SSominHUN/NESDev/Thesis/figures/Mario-Duckhunt-cartage.jpg

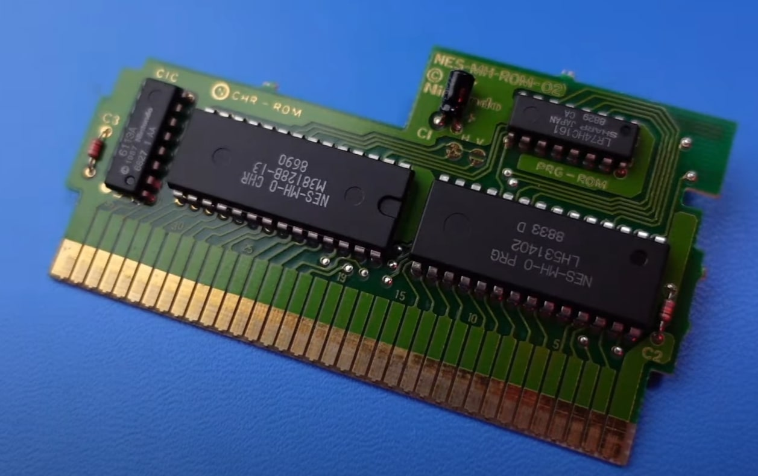
Thesis/figures/Mario-Duckhunt-cartage.jpg
