SSominHUN/NESDev/Thesis/figures/Mario-Patterns.jpg

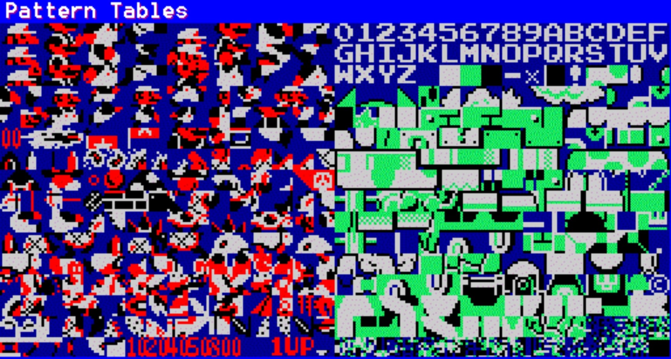
Thesis/figures/Mario-Patterns.jpg
