SSominHUN/NESDev/Thesis/figures/NES-motherboard-lines.jpg

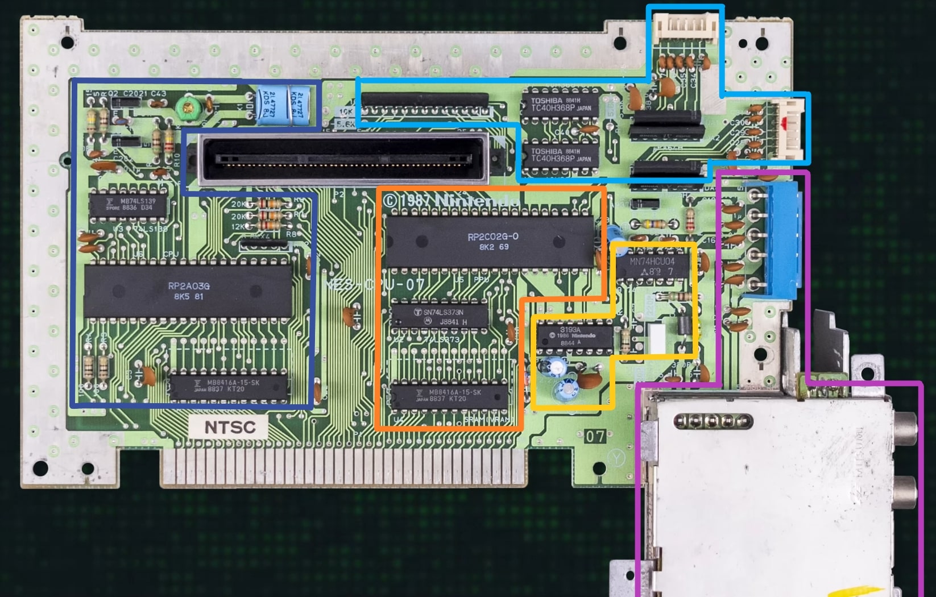
Thesis/figures/NES-motherboard-lines.jpg
