SSominHUN/NESDev/Thesis/figures/sprite-rendering-FSM-v2.png

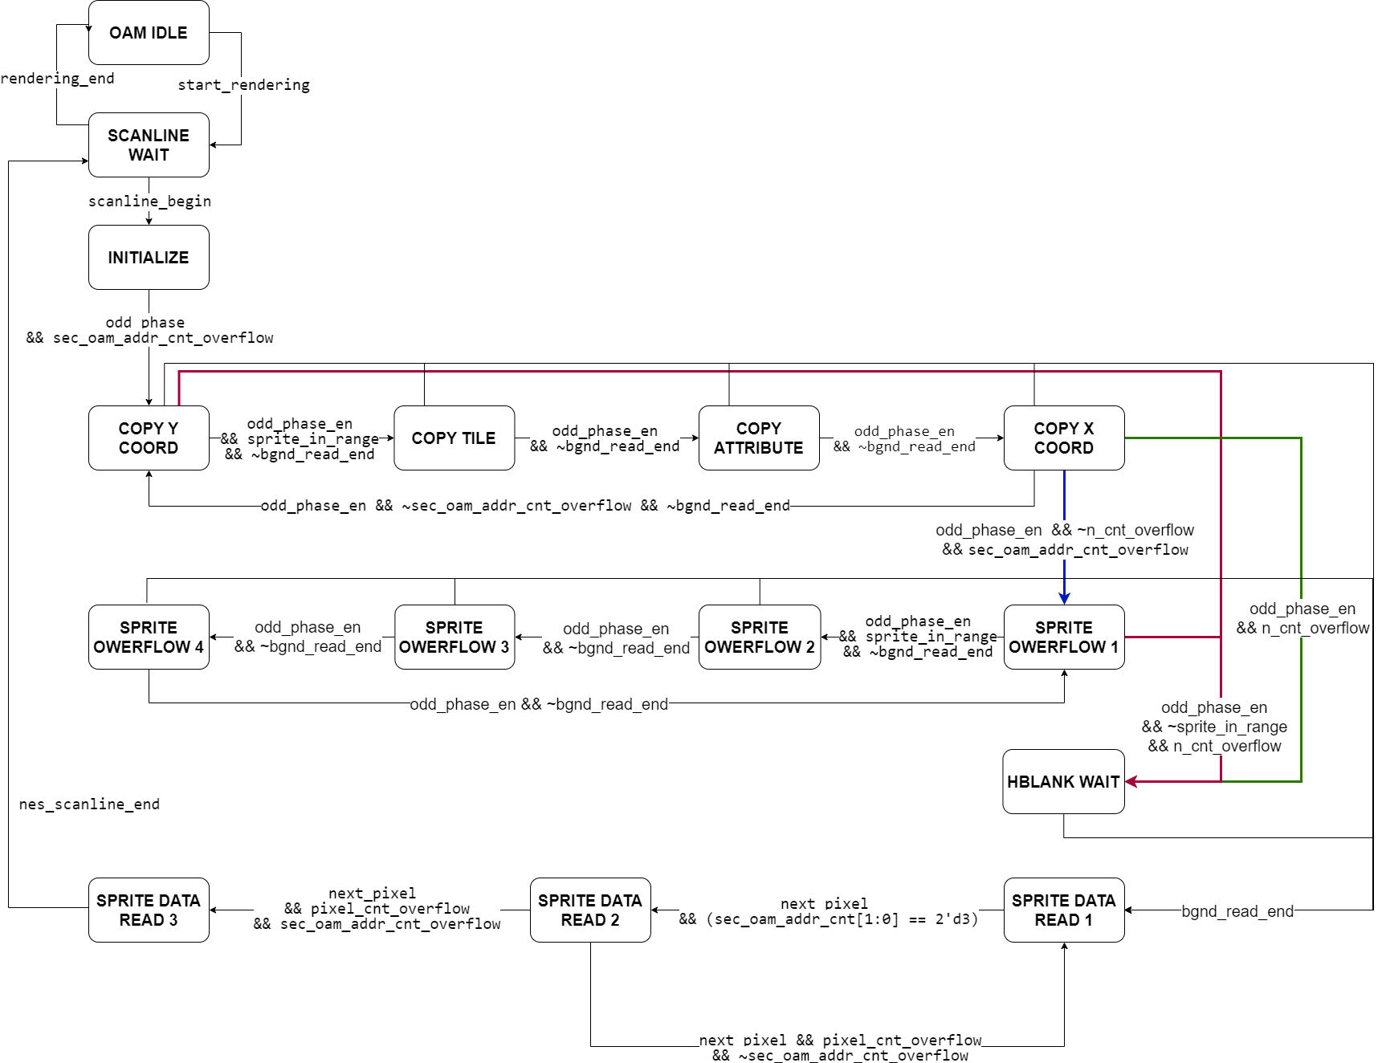
Thesis/figures/sprite-rendering-FSM-v2.png
