SSominHUN/NESDev/Thesis/figures/NES-components-top-1.png

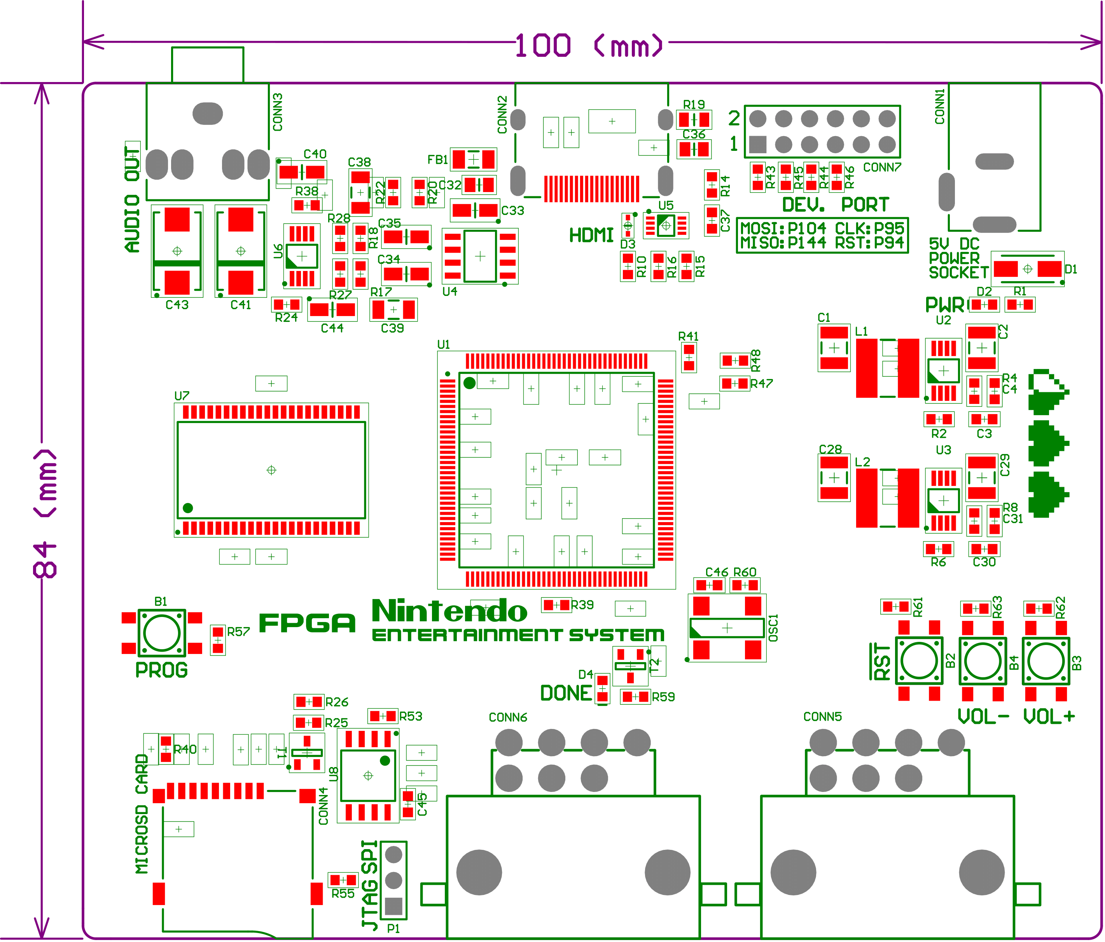
Thesis/figures/NES-components-top-1.png
