SSominHUN/NESDev/NES-pcb/Altium/Doc/FPGA_NES_SCH.PDF

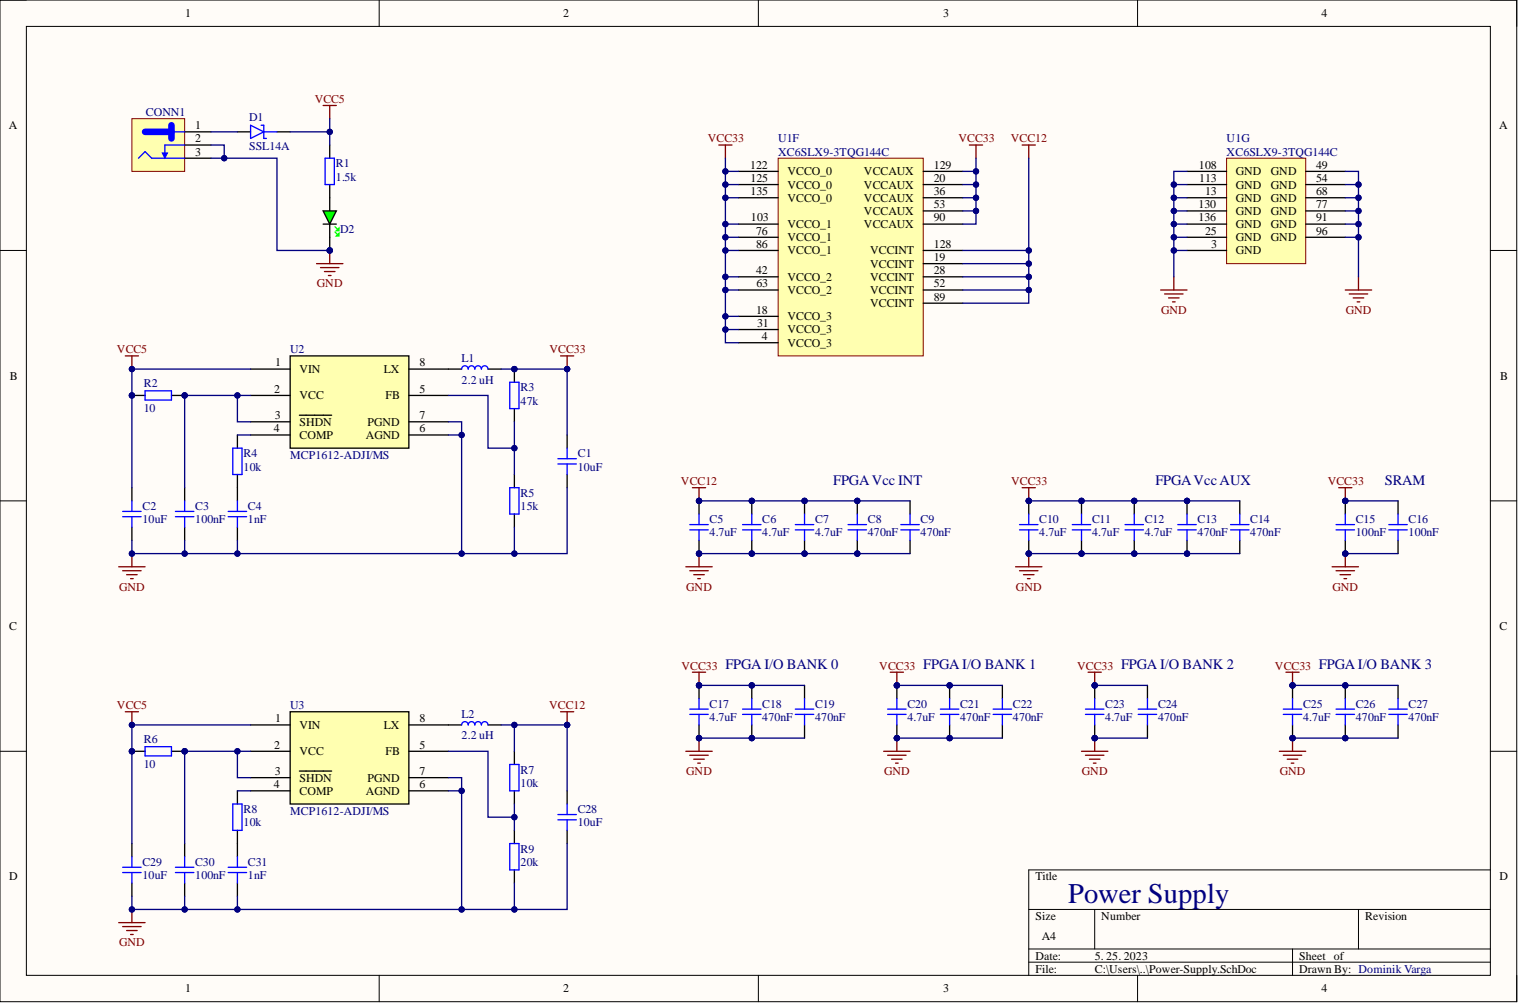
[picture p55: page 1]

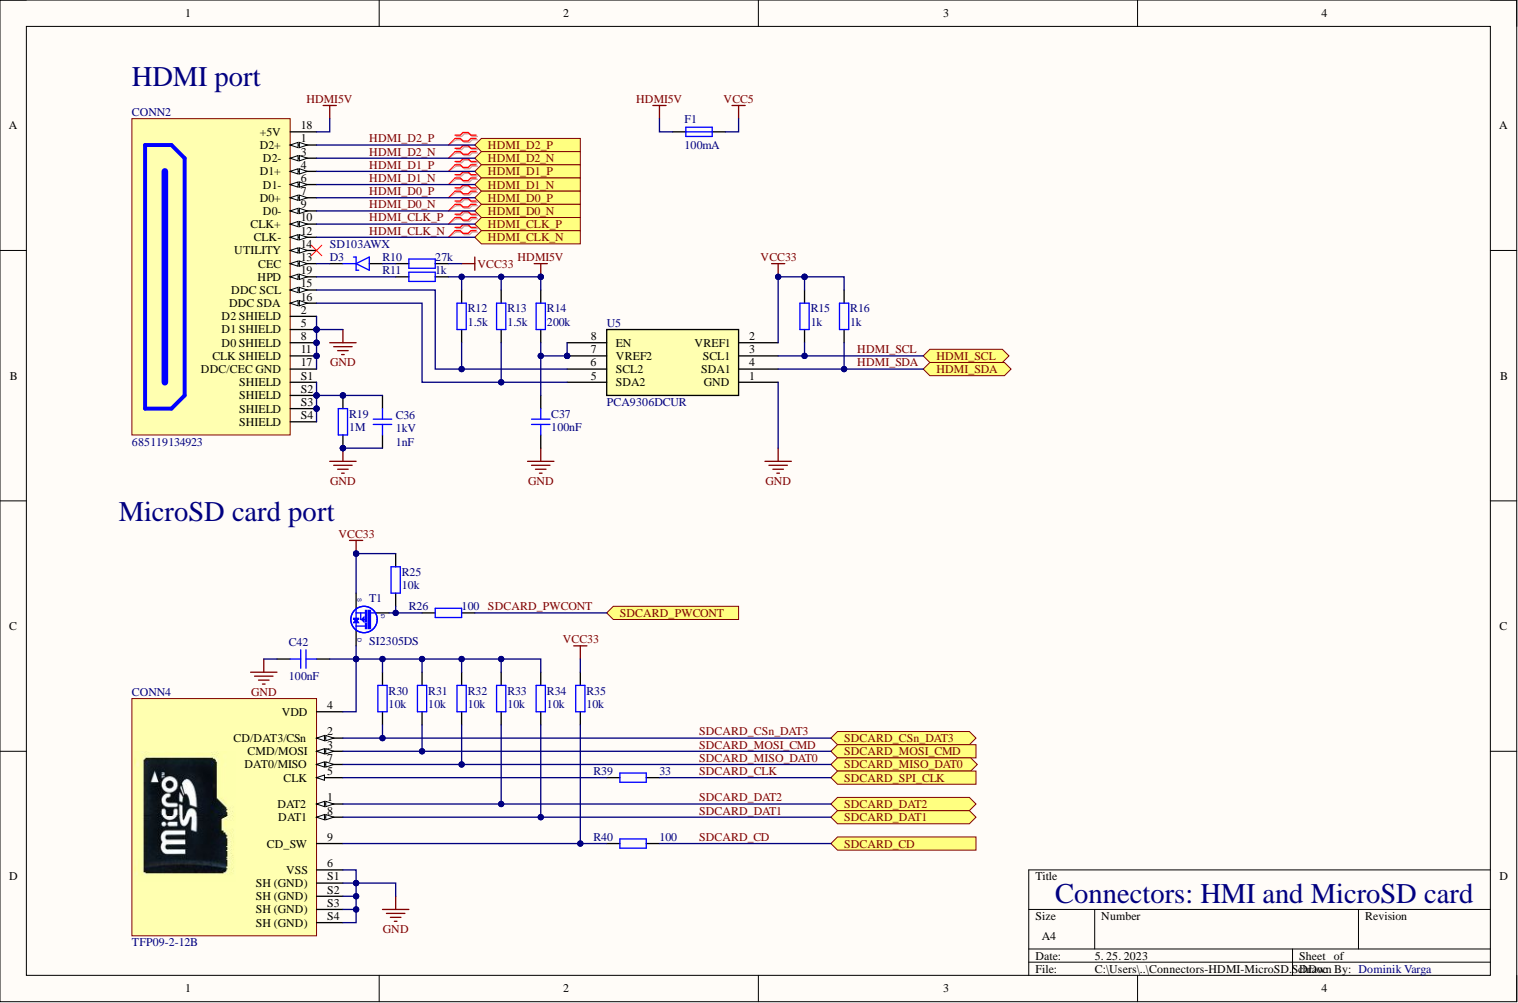
[picture p56: page 2]

Title
Connectors: HMI and MicroSD card

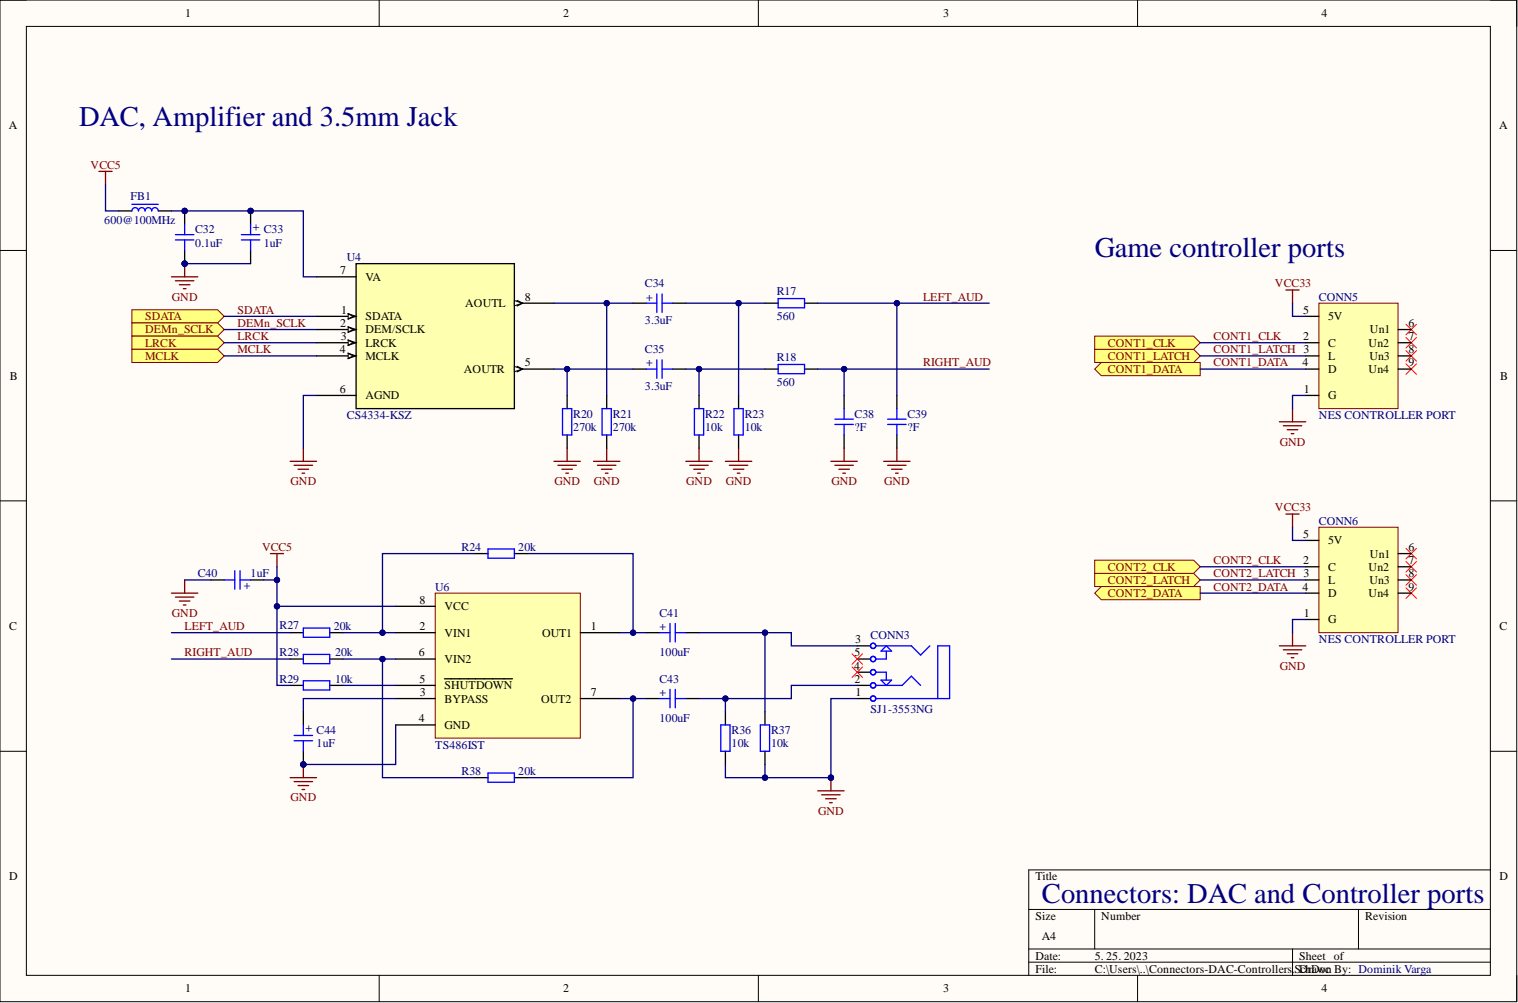
[picture p57: page 3]

DAC, Amplifier and 3.5mm Jack

VCC 8

VIN2 6 | C43

SHUTDOWN 5
BYPASS 3

GND 4

Title
Connectors: DAC and Controller ports

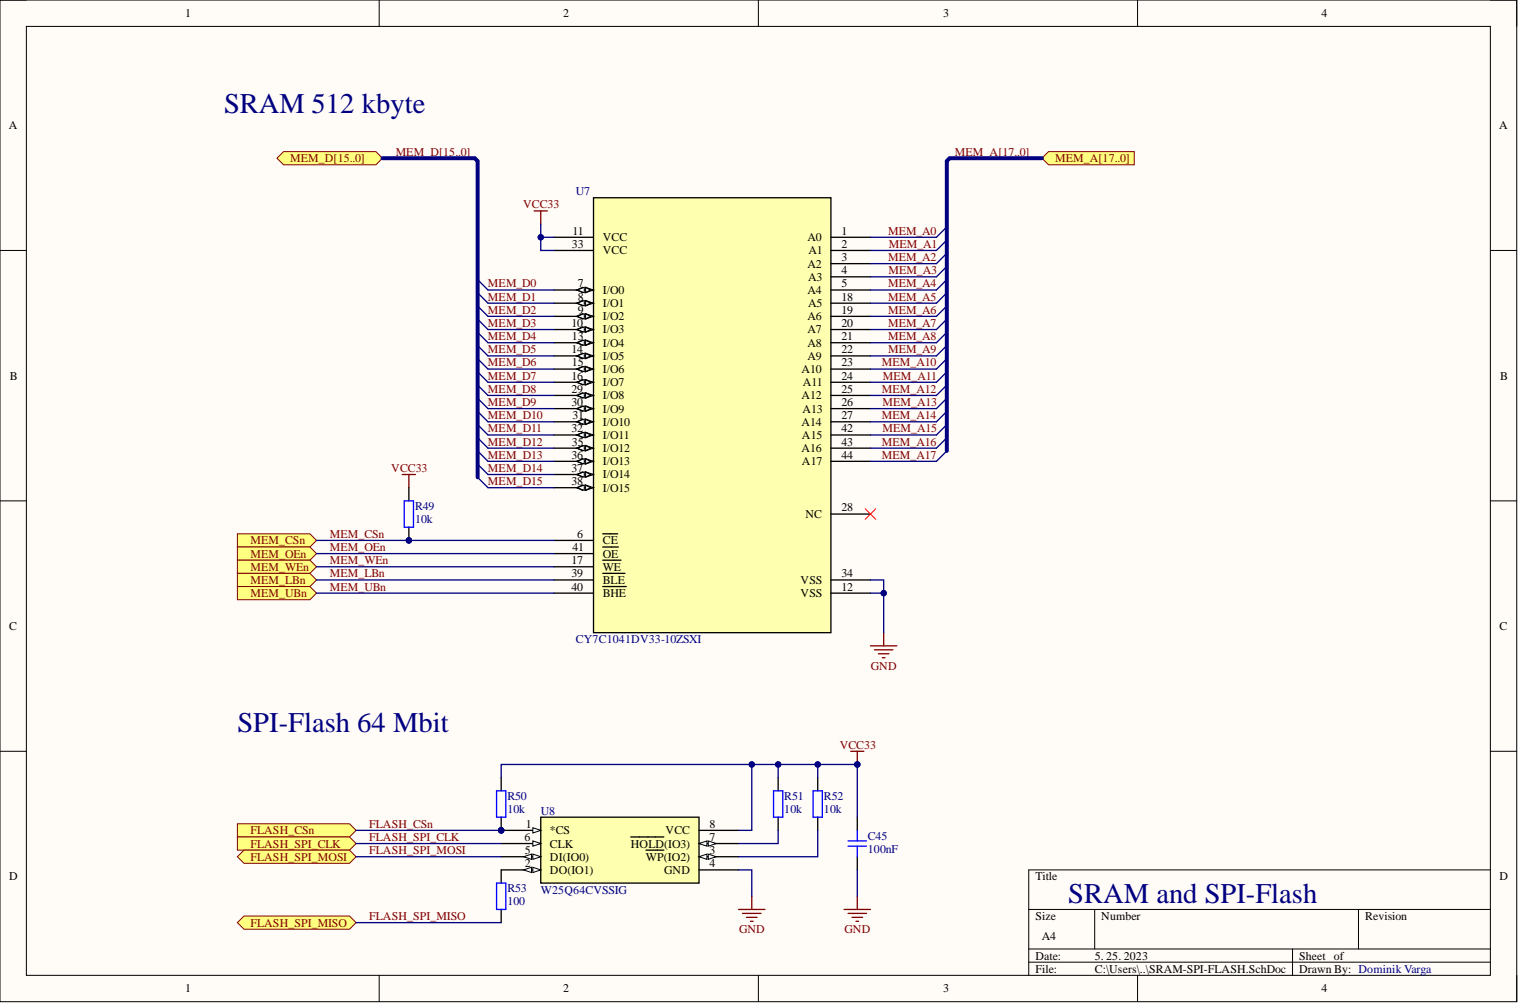
[picture p58: page 4]

Title
SRAM and SPI-Flash

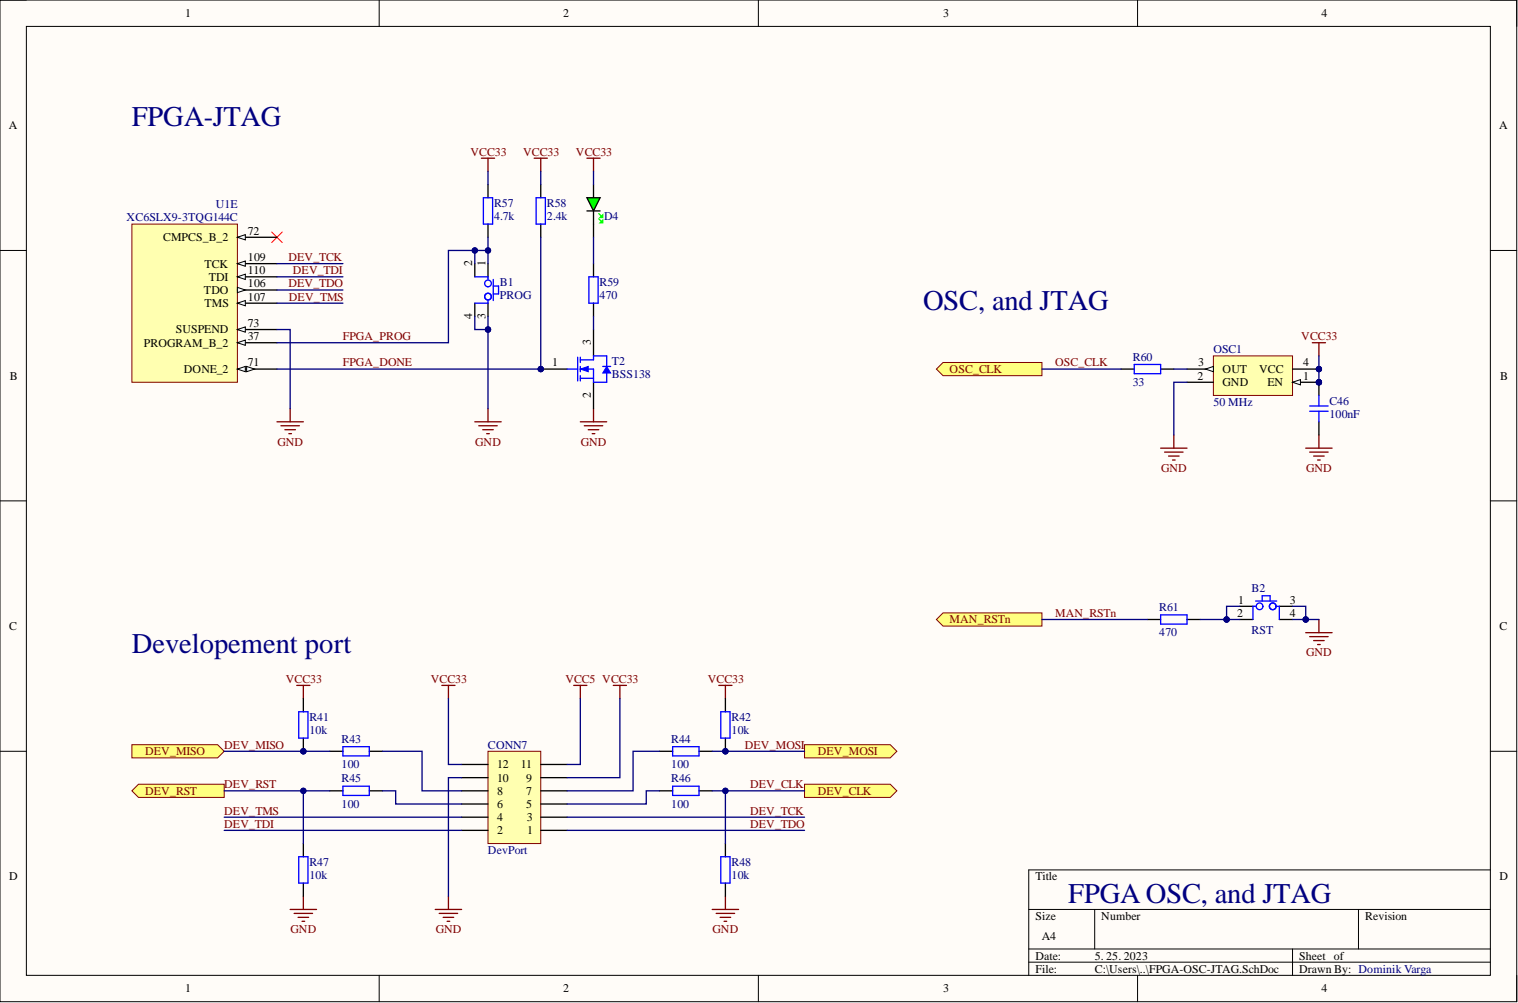
[picture p59: page 5]

FPGA_DONE

GND 2

Title
FPGA OSC, and JTAG

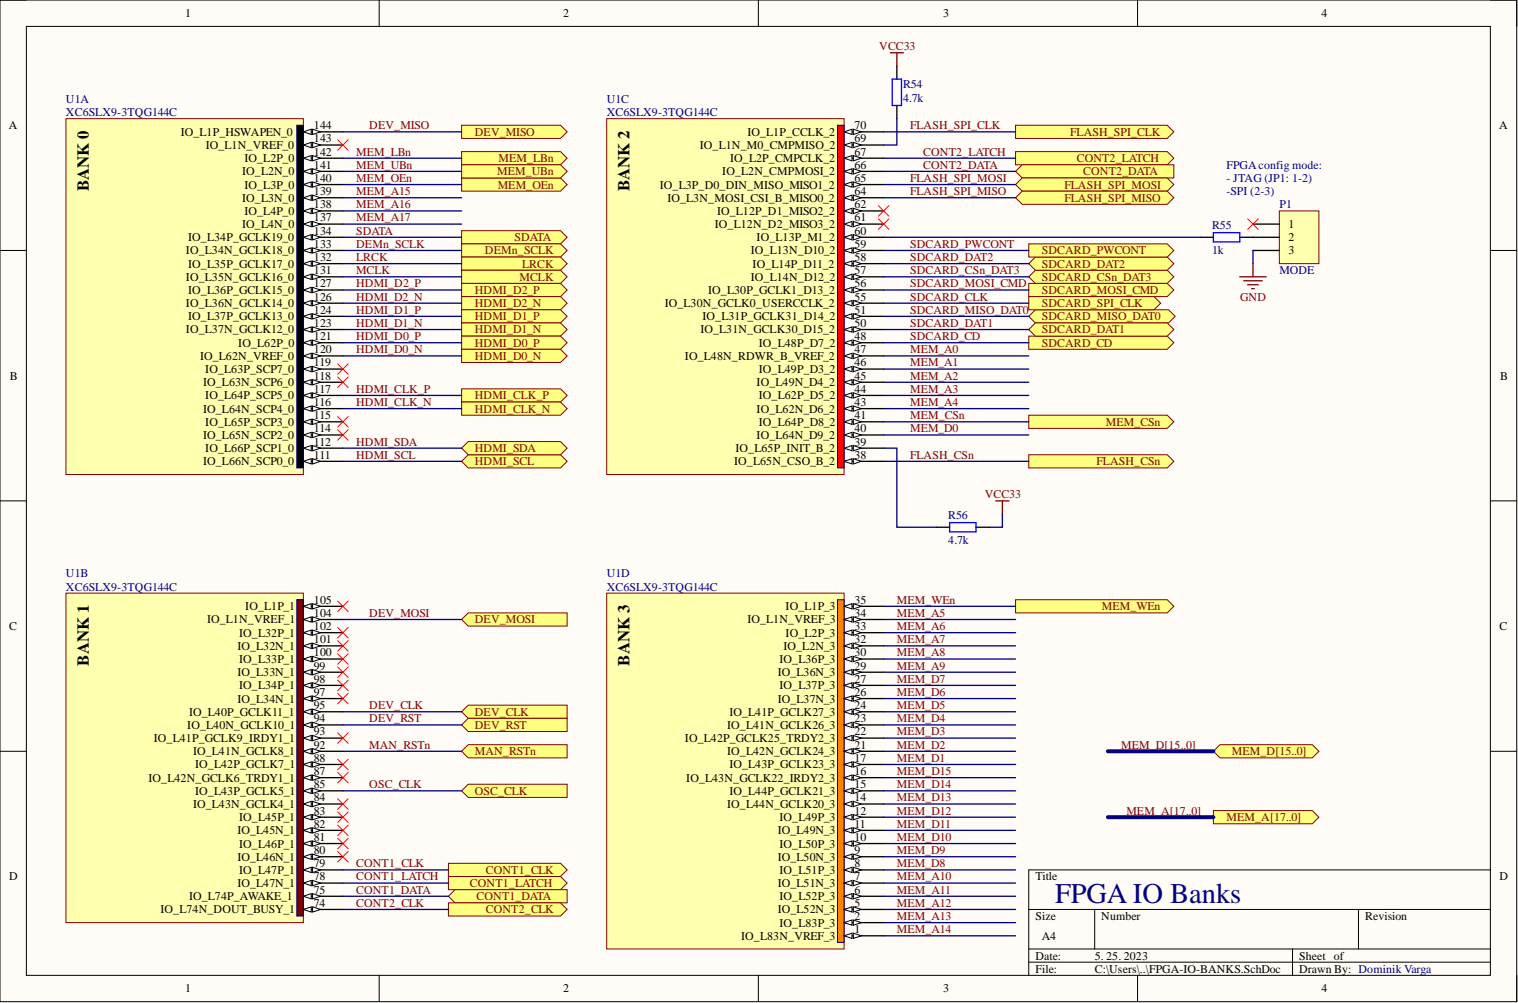
[picture p60: page 6]
