SSominHUN/NESDev/NES_hw/NES_fpga_hw/src/cpu/nes_cpu_test.v

////////////////////////////////////////////////////////////////////////////////
// Copyright (c) 1995-2013 Xilinx, Inc.  All rights reserved.
////////////////////////////////////////////////////////////////////////////////
//   ____  ____
//  /   /\/   /
// /___/  \  /    Vendor: Xilinx
// \   \   \/     Version: P.20131013
//  \   \         Application: netgen
//  /   /         Filename: nes_cpu_test.v
// /___/   /\     Timestamp: Wed Nov 01 00:47:12 2023
// \   \  /  \ 
//  \___\/\___\
//             
// Command	: -ofmt verilog -sim -w -dir D:\NESDev\NES_hw\NES_fpga_hw\src\cpu D:\NESDev\NES_hw\NES_fpga_hw\src\cpu\nes_cpu6502.ngc nes_cpu_test.v 
// Device	: xc6slx9-2-tqg144
// Input file	: D:/NESDev/NES_hw/NES_fpga_hw/src/cpu/nes_cpu6502.ngc
// Output file	: D:\NESDev\NES_hw\NES_fpga_hw\src\cpu\nes_cpu_test.v
// # of Modules	: 1
// Design Name	: nes_cpu6502
// Xilinx        : D:\Xilinx\14.7\ISE_DS\ISE\
//             
// Purpose:    
//     This verilog netlist is a verification model and uses simulation 
//     primitives which may not represent the true implementation of the 
//     device, however the netlist is functionally correct and should not 
//     be modified. This file cannot be synthesized and should only be used 
//     with supported simulation tools.
//             
// Reference:  
//     Command Line Tools User Guide, Chapter 23 and Synthesis and Simulation Design Guide, Chapter 6
//             
////////////////////////////////////////////////////////////////////////////////

`timescale 1 ns/1 ps

module nes_cpu6502 (
  clk, rst, ph1_rising, ph1_falling, ph2_rising, ph2_falling, int_n, nmi_n, ready, mst_mem_rnw, mst_mem_din, mst_mem_address, mst_mem_dout
);
  input clk;
  input rst;
  input ph1_rising;
  input ph1_falling;
  input ph2_rising;
  input ph2_falling;
  input int_n;
  input nmi_n;
  input ready;
  output mst_mem_rnw;
  input [7 : 0] mst_mem_din;
  output [15 : 0] mst_mem_address;
  output [7 : 0] mst_mem_dout;
  wire \NlwRenamedSig_OI_cpu6502/controller/mem_rnw ;
  wire N0;
  wire N1;
  wire \cpu6502/decoder/_n0035 ;
  wire \cpu6502/decoder/_n0040_0 ;
  wire \cpu6502/Reset_OR_DriverANDClockEnable ;
  wire \cpu6502/ph2_falling_mem_din_reg_we_AND_63_o ;
  wire \cpu6502/alu_en ;
  wire \cpu6502/data_out_sel[2]_GND_2_o_wide_mux_12_OUT<0> ;
  wire \cpu6502/data_out_sel[2]_GND_2_o_wide_mux_12_OUT<1> ;
  wire \cpu6502/data_out_sel[2]_GND_2_o_wide_mux_12_OUT<2> ;
  wire \cpu6502/data_out_sel[2]_GND_2_o_wide_mux_12_OUT<3> ;
  wire \cpu6502/data_out_sel[2]_GND_2_o_wide_mux_12_OUT<4> ;
  wire \cpu6502/data_out_sel[2]_GND_2_o_wide_mux_12_OUT<5>_54 ;
  wire \cpu6502/data_out_sel[2]_GND_2_o_wide_mux_12_OUT<6> ;
  wire \cpu6502/data_out_sel[2]_GND_2_o_wide_mux_12_OUT<7> ;
  wire \cpu6502/address_sel[1]_addr_zp[15]_wide_mux_6_OUT<0> ;
  wire \cpu6502/address_sel[1]_addr_zp[15]_wide_mux_6_OUT<1> ;
  wire \cpu6502/address_sel[1]_addr_zp[15]_wide_mux_6_OUT<2> ;
  wire \cpu6502/address_sel[1]_addr_zp[15]_wide_mux_6_OUT<3> ;
  wire \cpu6502/address_sel[1]_addr_zp[15]_wide_mux_6_OUT<4> ;
  wire \cpu6502/address_sel[1]_addr_zp[15]_wide_mux_6_OUT<5> ;
  wire \cpu6502/address_sel[1]_addr_zp[15]_wide_mux_6_OUT<6> ;
  wire \cpu6502/address_sel[1]_addr_zp[15]_wide_mux_6_OUT<7> ;
  wire \cpu6502/address_sel[1]_addr_zp[15]_wide_mux_6_OUT<8> ;
  wire \cpu6502/address_sel[1]_addr_zp[15]_wide_mux_6_OUT<9> ;
  wire \cpu6502/address_sel[1]_addr_zp[15]_wide_mux_6_OUT<10> ;
  wire \cpu6502/address_sel[1]_addr_zp[15]_wide_mux_6_OUT<11> ;
  wire \cpu6502/address_sel[1]_addr_zp[15]_wide_mux_6_OUT<12> ;
  wire \cpu6502/address_sel[1]_addr_zp[15]_wide_mux_6_OUT<13> ;
  wire \cpu6502/address_sel[1]_addr_zp[15]_wide_mux_6_OUT<14> ;
  wire \cpu6502/address_sel[1]_addr_zp[15]_wide_mux_6_OUT<15> ;
  wire \cpu6502/alu/c_flag_81 ;
  wire \cpu6502/alu/z_flag_82 ;
  wire \cpu6502/alu/i_flag_83 ;
  wire \cpu6502/alu/d_flag_84 ;
  wire \cpu6502/alu/v_flag_85 ;
  wire \cpu6502/alu/n_flag_86 ;
  wire \cpu6502/pc/pc_8_119 ;
  wire \cpu6502/pc/pc_9_120 ;
  wire \cpu6502/pc/pc_10_121 ;
  wire \cpu6502/pc/pc_11_122 ;
  wire \cpu6502/pc/pc_12_123 ;
  wire \cpu6502/pc/pc_13_124 ;
  wire \cpu6502/pc/pc_14_125 ;
  wire \cpu6502/pc/pc_15_126 ;
  wire \cpu6502/controller/set_next_state_127 ;
  wire \cpu6502/controller/b_flag_value_128 ;
  wire \cpu6502/controller/set_i_flag_129 ;
  wire \cpu6502/controller/mem_din_reg_we_130 ;
  wire \cpu6502/controller/alu_enable_131 ;
  wire \cpu6502/controller/inst_reg_we_143 ;
  wire \cpu6502/controller/inst_reg_clr_144 ;
  wire \cpu6502/controller/no_pcl_carry_reg_145 ;
  wire \cpu6502/controller/current_state_FSM_FFd11_148 ;
  wire \cpu6502/addr_gen/address_carry_165 ;
  wire \cpu6502/sreg_to_dout ;
  wire \cpu6502/branch_flag_val ;
  wire \cpu6502/index_reg_sel ;
  wire \cpu6502/addr_gen/addr2_h_reg[7]_GND_7_o_mux_23_OUT<3>_bdd0 ;
  wire \cpu6502/addr_gen/Madd_addr1_reg[7]_addr1_value_to_add[7]_add_2_OUT_lut<7>_239 ;
  wire \cpu6502/addr_gen/Madd_addr1_reg[7]_addr1_value_to_add[7]_add_2_OUT_cy<6>_240 ;
  wire \cpu6502/addr_gen/Madd_addr1_reg[7]_addr1_value_to_add[7]_add_2_OUT_lut<6>_241 ;
  wire \cpu6502/addr_gen/Madd_addr1_reg[7]_addr1_value_to_add[7]_add_2_OUT_cy<5>_242 ;
  wire \cpu6502/addr_gen/Madd_addr1_reg[7]_addr1_value_to_add[7]_add_2_OUT_lut<5>_243 ;
  wire \cpu6502/addr_gen/Madd_addr1_reg[7]_addr1_value_to_add[7]_add_2_OUT_cy<4>_244 ;
  wire \cpu6502/addr_gen/Madd_addr1_reg[7]_addr1_value_to_add[7]_add_2_OUT_lut<4>_245 ;
  wire \cpu6502/addr_gen/Madd_addr1_reg[7]_addr1_value_to_add[7]_add_2_OUT_cy<3>_246 ;
  wire \cpu6502/addr_gen/Madd_addr1_reg[7]_addr1_value_to_add[7]_add_2_OUT_lut<3>_247 ;
  wire \cpu6502/addr_gen/Madd_addr1_reg[7]_addr1_value_to_add[7]_add_2_OUT_cy<2>_248 ;
  wire \cpu6502/addr_gen/Madd_addr1_reg[7]_addr1_value_to_add[7]_add_2_OUT_lut<2>_249 ;
  wire \cpu6502/addr_gen/Madd_addr1_reg[7]_addr1_value_to_add[7]_add_2_OUT_cy<1>_250 ;
  wire \cpu6502/addr_gen/Madd_addr1_reg[7]_addr1_value_to_add[7]_add_2_OUT_lut<1>_251 ;
  wire \cpu6502/addr_gen/Madd_addr1_reg[7]_addr1_value_to_add[7]_add_2_OUT_cy<0>_252 ;
  wire \cpu6502/addr_gen/Madd_addr1_reg[7]_addr1_value_to_add[7]_add_2_OUT_lut<0>_253 ;
  wire \cpu6502/addr_gen/_n0086_inv ;
  wire \cpu6502/addr_gen/_n0102_inv ;
  wire \cpu6502/addr_gen/_n0094_inv ;
  wire \cpu6502/addr_gen/_n0080_inv ;
  wire \cpu6502/addr_gen/address_carry_GND_7_o_MUX_198_o ;
  wire \cpu6502/addr_gen/addr1_reg[7]_addr1_value_to_add[7]_add_2_OUT<0> ;
  wire \cpu6502/addr_gen/addr1_reg[7]_addr1_value_to_add[7]_add_2_OUT<1> ;
  wire \cpu6502/addr_gen/addr1_reg[7]_addr1_value_to_add[7]_add_2_OUT<2> ;
  wire \cpu6502/addr_gen/addr1_reg[7]_addr1_value_to_add[7]_add_2_OUT<3> ;
  wire \cpu6502/addr_gen/addr1_reg[7]_addr1_value_to_add[7]_add_2_OUT<4> ;
  wire \cpu6502/addr_gen/addr1_reg[7]_addr1_value_to_add[7]_add_2_OUT<5> ;
  wire \cpu6502/addr_gen/addr1_reg[7]_addr1_value_to_add[7]_add_2_OUT<6> ;
  wire \cpu6502/addr_gen/addr1_reg[7]_addr1_value_to_add[7]_add_2_OUT<7> ;
  wire \cpu6502/addr_gen/addr2_h_reg[7]_GND_7_o_mux_23_OUT<0> ;
  wire \cpu6502/addr_gen/addr2_h_reg[7]_GND_7_o_mux_23_OUT<1> ;
  wire \cpu6502/addr_gen/addr2_h_reg[7]_GND_7_o_mux_23_OUT<2> ;
  wire \cpu6502/addr_gen/addr2_h_reg[7]_GND_7_o_mux_23_OUT<3> ;
  wire \cpu6502/addr_gen/addr2_h_reg[7]_GND_7_o_mux_23_OUT<4> ;
  wire \cpu6502/addr_gen/addr2_h_reg[7]_GND_7_o_mux_23_OUT<5>_280 ;
  wire \cpu6502/addr_gen/addr2_h_reg[7]_GND_7_o_mux_23_OUT<6>_281 ;
  wire \cpu6502/addr_gen/addr2_h_reg[7]_GND_7_o_mux_23_OUT<7>_282 ;
  wire \cpu6502/addr_gen/addr2_l_reg[7]_GND_7_o_mux_14_OUT<0> ;
  wire \cpu6502/addr_gen/addr2_l_reg[7]_GND_7_o_mux_14_OUT<1> ;
  wire \cpu6502/addr_gen/addr2_l_reg[7]_GND_7_o_mux_14_OUT<2> ;
  wire \cpu6502/addr_gen/addr2_l_reg[7]_GND_7_o_mux_14_OUT<3> ;
  wire \cpu6502/addr_gen/addr2_l_reg[7]_GND_7_o_mux_14_OUT<4> ;
  wire \cpu6502/addr_gen/addr2_l_reg[7]_GND_7_o_mux_14_OUT<5> ;
  wire \cpu6502/addr_gen/addr2_l_reg[7]_GND_7_o_mux_14_OUT<6> ;
  wire \cpu6502/addr_gen/addr2_l_reg[7]_GND_7_o_mux_14_OUT<7> ;
  wire \cpu6502/addr_gen/addr1_reg[7]_GND_7_o_mux_5_OUT<0> ;
  wire \cpu6502/addr_gen/addr1_reg[7]_GND_7_o_mux_5_OUT<1> ;
  wire \cpu6502/addr_gen/addr1_reg[7]_GND_7_o_mux_5_OUT<2> ;
  wire \cpu6502/addr_gen/addr1_reg[7]_GND_7_o_mux_5_OUT<3> ;
  wire \cpu6502/addr_gen/addr1_reg[7]_GND_7_o_mux_5_OUT<4> ;
  wire \cpu6502/addr_gen/addr1_reg[7]_GND_7_o_mux_5_OUT<5> ;
  wire \cpu6502/addr_gen/addr1_reg[7]_GND_7_o_mux_5_OUT<6> ;
  wire \cpu6502/addr_gen/addr1_reg[7]_GND_7_o_mux_5_OUT<7> ;
  wire \cpu6502/controller/current_state_address_sel<0>2_299 ;
  wire \cpu6502/controller/current_state_current_state[4]_GND_4_o_select_152_OUT<1>1_300 ;
  wire \cpu6502/controller/current_state_FSM_FFd7_301 ;
  wire \cpu6502/controller/current_state_FSM_FFd8_302 ;
  wire \cpu6502/controller/current_state_FSM_FFd19_303 ;
  wire \cpu6502/controller/current_state_FSM_FFd21_304 ;
  wire \cpu6502/controller/current_state_FSM_FFd1-In_305 ;
  wire \cpu6502/controller/current_state_FSM_FFd2-In ;
  wire \cpu6502/controller/current_state_FSM_FFd3-In ;
  wire \cpu6502/controller/current_state_FSM_FFd4-In ;
  wire \cpu6502/controller/current_state_FSM_FFd5-In ;
  wire \cpu6502/controller/current_state_FSM_FFd6-In ;
  wire \cpu6502/controller/current_state_FSM_FFd7-In ;
  wire \cpu6502/controller/current_state_FSM_FFd8-In ;
  wire \cpu6502/controller/current_state_FSM_FFd9-In_313 ;
  wire \cpu6502/controller/current_state_FSM_FFd10-In_314 ;
  wire \cpu6502/controller/current_state_FSM_FFd11-In_315 ;
  wire \cpu6502/controller/current_state_FSM_FFd12-In_316 ;
  wire \cpu6502/controller/current_state_FSM_FFd13-In_317 ;
  wire \cpu6502/controller/current_state_FSM_FFd14-In ;
  wire \cpu6502/controller/current_state_FSM_FFd15-In ;
  wire \cpu6502/controller/current_state_FSM_FFd16-In ;
  wire \cpu6502/controller/current_state_FSM_FFd17-In_321 ;
  wire \cpu6502/controller/current_state_FSM_FFd18-In_322 ;
  wire \cpu6502/controller/current_state_FSM_FFd19-In_323 ;
  wire \cpu6502/controller/current_state_FSM_FFd20-In ;
  wire \cpu6502/controller/current_state_FSM_FFd21-In ;
  wire \cpu6502/controller/current_state_FSM_FFd22-In_326 ;
  wire \cpu6502/controller/current_state_FSM_FFd23-In ;
  wire \cpu6502/controller/current_state_FSM_FFd24-In ;
  wire \cpu6502/controller/current_state_FSM_FFd25-In ;
  wire \cpu6502/controller/current_state_FSM_FFd20-In111 ;
  wire \cpu6502/controller/current_state_FSM_FFd25-In22 ;
  wire \cpu6502/controller/current_state_FSM_FFd16-In1 ;
  wire \cpu6502/controller/Mram_rst_active_PWR_4_o_wide_mux_92_OUT2 ;
  wire \cpu6502/controller/Mram_rst_active_PWR_4_o_wide_mux_92_OUT1 ;
  wire \cpu6502/controller/Reset_OR_DriverANDClockEnable2 ;
  wire \cpu6502/controller/Reset_OR_DriverANDClockEnable1_336 ;
  wire \cpu6502/controller/Reset_OR_DriverANDClockEnable ;
  wire \cpu6502/controller/current_state[4]_PWR_4_o_select_108_OUT<2> ;
  wire \cpu6502/controller/current_state[4]_PWR_4_o_select_83_OUT<3> ;
  wire \cpu6502/controller/current_state[4]_reduce_nor_174_o ;
  wire \cpu6502/controller/branch_taken ;
  wire \cpu6502/controller/current_state[4]_GND_4_o_select_152_OUT<1> ;
  wire \cpu6502/controller/current_state_FSM_FFd18_343 ;
  wire \cpu6502/controller/current_state[4]_GND_4_o_select_152_OUT<3> ;
  wire \cpu6502/controller/current_state[4]_GND_4_o_select_152_OUT<4> ;
  wire \cpu6502/controller/current_state[4]_GND_4_o_select_152_OUT<5> ;
  wire \cpu6502/controller/current_state[4]_GND_4_o_select_152_OUT<6> ;
  wire \cpu6502/controller/current_state[4]_GND_4_o_select_152_OUT<7> ;
  wire \cpu6502/controller/current_state[4]_GND_4_o_Select_62_o_349 ;
  wire \cpu6502/controller/_n0433 ;
  wire \cpu6502/controller/_n0425 ;
  wire \cpu6502/controller/current_state[4]_operation_type[2]_Select_182_o ;
  wire \cpu6502/controller/_n0437 ;
  wire \cpu6502/controller/current_state[4]_mem_operation[1]_Select_167_o ;
  wire \cpu6502/controller/_n0556 ;
  wire \cpu6502/controller/current_state_FSM_FFd12_356 ;
  wire \cpu6502/controller/current_state_FSM_FFd22_357 ;
  wire \cpu6502/controller/current_state_FSM_FFd23_358 ;
  wire \cpu6502/controller/is_interrupt ;
  wire \cpu6502/controller/operation_type[2]_PWR_4_o_equal_130_o ;
  wire \cpu6502/controller/operation_type[2]_PWR_4_o_equal_90_o ;
  wire \cpu6502/controller/addr_mode[2]_GND_4_o_equal_25_o ;
  wire \cpu6502/controller/ready_mem_rnw_OR_4_o ;
  wire \cpu6502/controller/int_n_INV_5_o ;
  wire \cpu6502/controller/ph2_rising_nmi_recognized_AND_11_o ;
  wire \cpu6502/controller/ph1_falling_set_next_state_AND_61_o ;
  wire \cpu6502/controller/ph1_falling_current_state[4]_AND_34_o ;
  wire \cpu6502/controller/rst_set_i_flag_OR_110_o ;
  wire \cpu6502/controller/nmi_recognized_369 ;
  wire \cpu6502/controller/nmi_active_370 ;
  wire \cpu6502/controller/int_active_371 ;
  wire \cpu6502/controller/nmi_sample_372 ;
  wire \cpu6502/controller/current_state_FSM_FFd10_373 ;
  wire \cpu6502/controller/current_state_FSM_FFd9_374 ;
  wire \cpu6502/controller/current_state_FSM_FFd15_375 ;
  wire \cpu6502/controller/current_state_FSM_FFd1_376 ;
  wire \cpu6502/controller/current_state_FSM_FFd2_377 ;
  wire \cpu6502/controller/current_state_FSM_FFd5_378 ;
  wire \cpu6502/controller/current_state_FSM_FFd6_379 ;
  wire \cpu6502/controller/current_state_FSM_FFd14_380 ;
  wire \cpu6502/controller/current_state_FSM_FFd13_381 ;
  wire \cpu6502/controller/current_state_FSM_FFd24_382 ;
  wire \cpu6502/controller/current_state_FSM_FFd25_383 ;
  wire \cpu6502/controller/current_state_FSM_FFd3_384 ;
  wire \cpu6502/controller/current_state_FSM_FFd4_385 ;
  wire \cpu6502/controller/current_state_FSM_FFd17_386 ;
  wire \cpu6502/controller/current_state_FSM_FFd16_387 ;
  wire \cpu6502/controller/current_state_FSM_FFd20_388 ;
  wire \cpu6502/controller/rst_active_389 ;
  wire \cpu6502/pc/pc_enable_GND_5_o_AND_67_o ;
  wire \cpu6502/pc/pc_enable_pc_operation[3]_AND_65_o ;
  wire \cpu6502/alu/Mmux_alu_negative_3_455 ;
  wire \cpu6502/alu/Mmux_alu_negative_4_456 ;
  wire \cpu6502/alu/Mcount_stack_ptr_reg8 ;
  wire \cpu6502/alu/Mcount_stack_ptr_reg7 ;
  wire \cpu6502/alu/Mcount_stack_ptr_reg_mand6 ;
  wire \cpu6502/alu/Mcount_stack_ptr_reg6 ;
  wire \cpu6502/alu/Mcount_stack_ptr_reg_mand5 ;
  wire \cpu6502/alu/Mcount_stack_ptr_reg5 ;
  wire \cpu6502/alu/Mcount_stack_ptr_reg_mand4 ;
  wire \cpu6502/alu/Mcount_stack_ptr_reg4 ;
  wire \cpu6502/alu/Mcount_stack_ptr_reg_mand3 ;
  wire \cpu6502/alu/Mcount_stack_ptr_reg3 ;
  wire \cpu6502/alu/Mcount_stack_ptr_reg_mand2 ;
  wire \cpu6502/alu/Mcount_stack_ptr_reg2 ;
  wire \cpu6502/alu/Mcount_stack_ptr_reg_mand1 ;
  wire \cpu6502/alu/Mcount_stack_ptr_reg1_500 ;
  wire \cpu6502/alu/Mcount_stack_ptr_reg_mand_501 ;
  wire \cpu6502/alu/dest_reg_sel[2]_PWR_6_o_equal_44_o_inv ;
  wire \cpu6502/alu/Mcount_stack_ptr_reg ;
  wire \cpu6502/alu/_n0199_inv_504 ;
  wire \cpu6502/alu/_n0221_inv ;
  wire \cpu6502/alu/_n0237_inv ;
  wire \cpu6502/alu/_n0227_inv ;
  wire \cpu6502/alu/c_in ;
  wire \cpu6502/alu/dest_reg_sel[2]_PWR_6_o_equal_55_o ;
  wire \cpu6502/alu/n_flag_mem_in[7]_MUX_185_o ;
  wire \cpu6502/alu/status_op[1]_mem_in[6]_MUX_181_o ;
  wire \cpu6502/alu/status_op[1]_mem_in[3]_MUX_176_o ;
  wire \cpu6502/alu/status_op[1]_mem_in[2]_MUX_171_o ;
  wire \cpu6502/alu/z_flag_mem_in[1]_MUX_166_o ;
  wire \cpu6502/alu/status_op[1]_mem_in[0]_MUX_162_o ;
  wire \cpu6502/alu/alu_enable_dest_reg_sel[2]_AND_87_o ;
  wire \cpu6502/alu/alu_enable_dest_reg_sel[2]_AND_86_o ;
  wire \cpu6502/alu/alu_enable_dest_reg_sel[2]_AND_85_o ;
  wire \cpu6502/data_out_sel[2]_GND_2_o_wide_mux_12_OUT<1>1_559 ;
  wire \cpu6502/data_out_sel[2]_GND_2_o_wide_mux_12_OUT<1>2_560 ;
  wire \cpu6502/data_out_sel[2]_GND_2_o_wide_mux_12_OUT<2>1_561 ;
  wire \cpu6502/data_out_sel[2]_GND_2_o_wide_mux_12_OUT<2>2_562 ;
  wire \cpu6502/data_out_sel[2]_GND_2_o_wide_mux_12_OUT<3>1_563 ;
  wire \cpu6502/data_out_sel[2]_GND_2_o_wide_mux_12_OUT<3>2_564 ;
  wire \cpu6502/data_out_sel[2]_GND_2_o_wide_mux_12_OUT<4>1_565 ;
  wire \cpu6502/data_out_sel[2]_GND_2_o_wide_mux_12_OUT<4>2_566 ;
  wire \cpu6502/data_out_sel[2]_GND_2_o_wide_mux_12_OUT<6>1_567 ;
  wire \cpu6502/data_out_sel[2]_GND_2_o_wide_mux_12_OUT<6>2_568 ;
  wire \cpu6502/data_out_sel[2]_GND_2_o_wide_mux_12_OUT<7>1_569 ;
  wire \cpu6502/data_out_sel[2]_GND_2_o_wide_mux_12_OUT<7>2_570 ;
  wire N4;
  wire N6;
  wire N8;
  wire N10;
  wire N12;
  wire N18;
  wire N20;
  wire N22;
  wire \cpu6502/controller/current_state_current_state[4]_PWR_4_o_select_83_OUT<3> ;
  wire \cpu6502/controller/current_state_current_state[4]_PWR_4_o_select_83_OUT<3>1_580 ;
  wire \cpu6502/controller/current_state_current_state[4]_PWR_4_o_select_83_OUT<3>2_581 ;
  wire \cpu6502/controller/current_state_current_state[4]_PWR_4_o_select_83_OUT<3>3_582 ;
  wire N24;
  wire \cpu6502/controller/current_state_address_sel<0>1_585 ;
  wire \cpu6502/controller/current_state_current_state[4]_GND_4_o_select_152_OUT<4> ;
  wire N26;
  wire \cpu6502/controller/current_state_FSM_FFd6-In1_588 ;
  wire N28;
  wire N30;
  wire \cpu6502/controller/current_state_FSM_FFd23-In1_591 ;
  wire N34;
  wire \cpu6502/controller/current_state_FSM_FFd21-In1_593 ;
  wire \cpu6502/controller/current_state_FSM_FFd21-In2_594 ;
  wire N36;
  wire \cpu6502/controller/current_state_FSM_FFd20-In1_596 ;
  wire \cpu6502/controller/current_state_FSM_FFd20-In2_597 ;
  wire \cpu6502/controller/current_state_FSM_FFd25-In1_598 ;
  wire \cpu6502/controller/current_state_FSM_FFd25-In2_599 ;
  wire \cpu6502/controller/current_state_FSM_FFd25-In3_600 ;
  wire \cpu6502/controller/current_state_FSM_FFd25-In4_601 ;
  wire \cpu6502/controller/current_state_FSM_FFd25-In5_602 ;
  wire N38;
  wire N40;
  wire N42;
  wire \cpu6502/alu/Mmux_alu_result8 ;
  wire \cpu6502/alu/Mmux_alu_result81_607 ;
  wire \cpu6502/alu/Mmux_status_op[1]_mem_in[6]_MUX_181_o1 ;
  wire \cpu6502/alu/Mmux_status_op[1]_mem_in[6]_MUX_181_o11_609 ;
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
  wire \NLW_cpu6502_decoder/Mram_instr_decoder_rom_DOB<23>_UNCONNECTED ;
  wire \NLW_cpu6502_decoder/Mram_instr_decoder_rom_DOB<22>_UNCONNECTED ;
  wire \NLW_cpu6502_decoder/Mram_instr_decoder_rom_DOB<21>_UNCONNECTED ;
  wire \NLW_cpu6502_decoder/Mram_instr_decoder_rom_DOB<20>_UNCONNECTED ;
  wire \NLW_cpu6502_decoder/Mram_instr_decoder_rom_DOB<19>_UNCONNECTED ;
  wire \NLW_cpu6502_decoder/Mram_instr_decoder_rom_DOB<18>_UNCONNECTED ;
  wire \NLW_cpu6502_decoder/Mram_instr_decoder_rom_DOB<17>_UNCONNECTED ;
  wire \NLW_cpu6502_decoder/Mram_instr_decoder_rom_DOB<16>_UNCONNECTED ;
  wire \NLW_cpu6502_decoder/Mram_instr_decoder_rom_DOB<15>_UNCONNECTED ;
  wire \NLW_cpu6502_decoder/Mram_instr_decoder_rom_DOB<14>_UNCONNECTED ;
  wire \NLW_cpu6502_decoder/Mram_instr_decoder_rom_DOB<13>_UNCONNECTED ;
  wire \NLW_cpu6502_decoder/Mram_instr_decoder_rom_DOB<12>_UNCONNECTED ;
  wire \NLW_cpu6502_decoder/Mram_instr_decoder_rom_DOB<11>_UNCONNECTED ;
  wire \NLW_cpu6502_decoder/Mram_instr_decoder_rom_DOB<10>_UNCONNECTED ;
  wire \NLW_cpu6502_decoder/Mram_instr_decoder_rom_DOB<9>_UNCONNECTED ;
  wire \NLW_cpu6502_decoder/Mram_instr_decoder_rom_DOB<8>_UNCONNECTED ;
  wire \NLW_cpu6502_decoder/Mram_instr_decoder_rom_DOB<7>_UNCONNECTED ;
  wire \NLW_cpu6502_decoder/Mram_instr_decoder_rom_DOB<6>_UNCONNECTED ;
  wire \NLW_cpu6502_decoder/Mram_instr_decoder_rom_DOB<5>_UNCONNECTED ;
  wire \NLW_cpu6502_decoder/Mram_instr_decoder_rom_DOB<4>_UNCONNECTED ;
  wire \NLW_cpu6502_decoder/Mram_instr_decoder_rom_DOB<3>_UNCONNECTED ;
  wire \NLW_cpu6502_decoder/Mram_instr_decoder_rom_DOB<2>_UNCONNECTED ;
  wire \NLW_cpu6502_decoder/Mram_instr_decoder_rom_DOB<1>_UNCONNECTED ;
  wire \NLW_cpu6502_decoder/Mram_instr_decoder_rom_DOB<0>_UNCONNECTED ;
  wire \NLW_cpu6502_decoder/Mram_instr_decoder_rom_WEB<3>_UNCONNECTED ;
  wire \NLW_cpu6502_decoder/Mram_instr_decoder_rom_WEB<2>_UNCONNECTED ;
  wire \NLW_cpu6502_decoder/Mram_instr_decoder_rom_WEB<1>_UNCONNECTED ;
  wire \NLW_cpu6502_decoder/Mram_instr_decoder_rom_WEB<0>_UNCONNECTED ;
  wire [15 : 0] \cpu6502/mst_mem_address ;
  wire [7 : 0] \cpu6502/mst_mem_dout ;
  wire [7 : 0] \cpu6502/alu/result_reg ;
  wire [7 : 0] \cpu6502/alu/stack_ptr_reg ;
  wire [7 : 0] \cpu6502/alu/y_reg ;
  wire [7 : 0] \cpu6502/alu/x_reg ;
  wire [7 : 0] \cpu6502/pc/pc ;
  wire [7 : 0] \cpu6502/controller/addr_ctrl_signals ;
  wire [2 : 0] \cpu6502/controller/stack_ctrl_signals ;
  wire [1 : 0] \cpu6502/data_out_sel ;
  wire [1 : 0] \cpu6502/address_sel ;
  wire [2 : 1] \cpu6502/controller/vector_to_load ;
  wire [3 : 0] \cpu6502/controller/pc_operation ;
  wire [7 : 0] \cpu6502/mem_din_reg ;
  wire [7 : 0] \cpu6502/addr_gen/addr2_l_reg ;
  wire [7 : 0] \cpu6502/addr_gen/addr2_h_reg ;
  wire [7 : 0] \cpu6502/addr_gen/addr1_reg ;
  wire [5 : 0] \cpu6502/sreg_mask ;
  wire [1 : 0] \cpu6502/sreg_operation_sel ;
  wire [2 : 0] \cpu6502/alu_dest_reg_sel ;
  wire [2 : 0] \cpu6502/alu_operation_sel ;
  wire [1 : 0] \cpu6502/alu_cin_sel ;
  wire [1 : 0] \cpu6502/alu_operand2_sel ;
  wire [2 : 0] \cpu6502/alu_operand1_sel ;
  wire [2 : 0] \cpu6502/operation_type ;
  wire [1 : 0] \cpu6502/mem_operation ;
  wire [2 : 0] \cpu6502/addr_mode ;
  wire [7 : 0] \cpu6502/addr_gen/Madd_addr2_l_reg_in_cy ;
  wire [7 : 0] \cpu6502/addr_gen/Madd_addr2_l_reg_in_lut ;
  wire [7 : 0] \cpu6502/addr_gen/addr2_l_reg_in ;
  wire [7 : 0] \cpu6502/pc/Madd_incremented_pc_value_h_Madd_lut ;
  wire [6 : 0] \cpu6502/pc/Madd_incremented_pc_value_h_Madd_cy ;
  wire [7 : 0] \cpu6502/pc/Madd_n0067_cy ;
  wire [7 : 0] \cpu6502/pc/Madd_n0067_lut ;
  wire [7 : 0] \cpu6502/pc/incremented_pc_value_h ;
  wire [7 : 0] \cpu6502/pc/n0067 ;
  wire [15 : 0] \cpu6502/pc/value_to_load ;
  wire [7 : 0] \cpu6502/alu/Madd_n0137_Madd_cy ;
  wire [6 : 0] \cpu6502/alu/Madd_n0137_Madd_lut ;
  wire [7 : 0] \cpu6502/alu/Mcount_stack_ptr_reg_lut ;
  wire [6 : 0] \cpu6502/alu/Mcount_stack_ptr_reg_cy ;
  wire [7 : 0] \cpu6502/alu/n0137 ;
  wire [7 : 0] \cpu6502/alu/alu_result ;
  wire [7 : 0] \cpu6502/alu/accumulator ;
  wire [7 : 0] \cpu6502/alu/op1 ;
  wire [7 : 0] \cpu6502/alu/op2 ;
  wire [0 : 0] \cpu6502/controller/current_state_address_sel ;
  assign
    mst_mem_address[15] = \cpu6502/mst_mem_address [15],
    mst_mem_address[14] = \cpu6502/mst_mem_address [14],
    mst_mem_address[13] = \cpu6502/mst_mem_address [13],
    mst_mem_address[12] = \cpu6502/mst_mem_address [12],
    mst_mem_address[11] = \cpu6502/mst_mem_address [11],
    mst_mem_address[10] = \cpu6502/mst_mem_address [10],
    mst_mem_address[9] = \cpu6502/mst_mem_address [9],
    mst_mem_address[8] = \cpu6502/mst_mem_address [8],
    mst_mem_address[7] = \cpu6502/mst_mem_address [7],
    mst_mem_address[6] = \cpu6502/mst_mem_address [6],
    mst_mem_address[5] = \cpu6502/mst_mem_address [5],
    mst_mem_address[4] = \cpu6502/mst_mem_address [4],
    mst_mem_address[3] = \cpu6502/mst_mem_address [3],
    mst_mem_address[2] = \cpu6502/mst_mem_address [2],
    mst_mem_address[1] = \cpu6502/mst_mem_address [1],
    mst_mem_address[0] = \cpu6502/mst_mem_address [0],
    mst_mem_dout[7] = \cpu6502/mst_mem_dout [7],
    mst_mem_dout[6] = \cpu6502/mst_mem_dout [6],
    mst_mem_dout[5] = \cpu6502/mst_mem_dout [5],
    mst_mem_dout[4] = \cpu6502/mst_mem_dout [4],
    mst_mem_dout[3] = \cpu6502/mst_mem_dout [3],
    mst_mem_dout[2] = \cpu6502/mst_mem_dout [2],
    mst_mem_dout[1] = \cpu6502/mst_mem_dout [1],
    mst_mem_dout[0] = \cpu6502/mst_mem_dout [0],
    mst_mem_rnw = \NlwRenamedSig_OI_cpu6502/controller/mem_rnw ;
  GND   XST_GND (
    .G(N0)
  );
  VCC   XST_VCC (
    .P(N1)
  );
  FDRE   \cpu6502/mst_mem_address_15  (
    .C(clk),
    .CE(ph1_rising),
    .D(\cpu6502/address_sel[1]_addr_zp[15]_wide_mux_6_OUT<15> ),
    .R(rst),
    .Q(\cpu6502/mst_mem_address [15])
  );
  FDRE   \cpu6502/mst_mem_address_14  (
    .C(clk),
    .CE(ph1_rising),
    .D(\cpu6502/address_sel[1]_addr_zp[15]_wide_mux_6_OUT<14> ),
    .R(rst),
    .Q(\cpu6502/mst_mem_address [14])
  );
  FDRE   \cpu6502/mst_mem_address_13  (
    .C(clk),
    .CE(ph1_rising),
    .D(\cpu6502/address_sel[1]_addr_zp[15]_wide_mux_6_OUT<13> ),
    .R(rst),
    .Q(\cpu6502/mst_mem_address [13])
  );
  FDRE   \cpu6502/mst_mem_address_12  (
    .C(clk),
    .CE(ph1_rising),
    .D(\cpu6502/address_sel[1]_addr_zp[15]_wide_mux_6_OUT<12> ),
    .R(rst),
    .Q(\cpu6502/mst_mem_address [12])
  );
  FDRE   \cpu6502/mst_mem_address_11  (
    .C(clk),
    .CE(ph1_rising),
    .D(\cpu6502/address_sel[1]_addr_zp[15]_wide_mux_6_OUT<11> ),
    .R(rst),
    .Q(\cpu6502/mst_mem_address [11])
  );
  FDRE   \cpu6502/mst_mem_address_10  (
    .C(clk),
    .CE(ph1_rising),
    .D(\cpu6502/address_sel[1]_addr_zp[15]_wide_mux_6_OUT<10> ),
    .R(rst),
    .Q(\cpu6502/mst_mem_address [10])
  );
  FDRE   \cpu6502/mst_mem_address_9  (
    .C(clk),
    .CE(ph1_rising),
    .D(\cpu6502/address_sel[1]_addr_zp[15]_wide_mux_6_OUT<9> ),
    .R(rst),
    .Q(\cpu6502/mst_mem_address [9])
  );
  FDRE   \cpu6502/mst_mem_address_8  (
    .C(clk),
    .CE(ph1_rising),
    .D(\cpu6502/address_sel[1]_addr_zp[15]_wide_mux_6_OUT<8> ),
    .R(rst),
    .Q(\cpu6502/mst_mem_address [8])
  );
  FDRE   \cpu6502/mst_mem_address_7  (
    .C(clk),
    .CE(ph1_rising),
    .D(\cpu6502/address_sel[1]_addr_zp[15]_wide_mux_6_OUT<7> ),
    .R(rst),
    .Q(\cpu6502/mst_mem_address [7])
  );
  FDRE   \cpu6502/mst_mem_address_6  (
    .C(clk),
    .CE(ph1_rising),
    .D(\cpu6502/address_sel[1]_addr_zp[15]_wide_mux_6_OUT<6> ),
    .R(rst),
    .Q(\cpu6502/mst_mem_address [6])
  );
  FDRE   \cpu6502/mst_mem_address_5  (
    .C(clk),
    .CE(ph1_rising),
    .D(\cpu6502/address_sel[1]_addr_zp[15]_wide_mux_6_OUT<5> ),
    .R(rst),
    .Q(\cpu6502/mst_mem_address [5])
  );
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
    .CI(\cpu6502/addr_gen/Madd_addr2_l_reg_in_cy [0]),
    .LI(\cpu6502/addr_gen/Madd_addr2_l_reg_in_lut [1]),
    .O(\cpu6502/addr_gen/addr2_l_reg_in [1])
  );
  MUXCY   \cpu6502/addr_gen/Madd_addr2_l_reg_in_cy<1>  (
    .CI(\cpu6502/addr_gen/Madd_addr2_l_reg_in_cy [0]),
    .DI(\cpu6502/addr_gen/addr2_l_reg [1]),
    .S(\cpu6502/addr_gen/Madd_addr2_l_reg_in_lut [1]),
    .O(\cpu6502/addr_gen/Madd_addr2_l_reg_in_cy [1])
  );
  XORCY   \cpu6502/addr_gen/Madd_addr2_l_reg_in_xor<0>  (
    .CI(N0),
    .LI(\cpu6502/addr_gen/Madd_addr2_l_reg_in_lut [0]),
    .O(\cpu6502/addr_gen/addr2_l_reg_in [0])
  );
  MUXCY   \cpu6502/addr_gen/Madd_addr2_l_reg_in_cy<0>  (
    .CI(N0),
    .DI(\cpu6502/addr_gen/addr2_l_reg [0]),
    .S(\cpu6502/addr_gen/Madd_addr2_l_reg_in_lut [0]),
    .O(\cpu6502/addr_gen/Madd_addr2_l_reg_in_cy [0])
  );
  XORCY   \cpu6502/addr_gen/Madd_addr1_reg[7]_addr1_value_to_add[7]_add_2_OUT_xor<7>  (
    .CI(\cpu6502/addr_gen/Madd_addr1_reg[7]_addr1_value_to_add[7]_add_2_OUT_cy<6>_240 ),
    .LI(\cpu6502/addr_gen/Madd_addr1_reg[7]_addr1_value_to_add[7]_add_2_OUT_lut<7>_239 ),
    .O(\cpu6502/addr_gen/addr1_reg[7]_addr1_value_to_add[7]_add_2_OUT<7> )
  );
  XORCY   \cpu6502/addr_gen/Madd_addr1_reg[7]_addr1_value_to_add[7]_add_2_OUT_xor<6>  (
    .CI(\cpu6502/addr_gen/Madd_addr1_reg[7]_addr1_value_to_add[7]_add_2_OUT_cy<5>_242 ),
    .LI(\cpu6502/addr_gen/Madd_addr1_reg[7]_addr1_value_to_add[7]_add_2_OUT_lut<6>_241 ),
    .O(\cpu6502/addr_gen/addr1_reg[7]_addr1_value_to_add[7]_add_2_OUT<6> )
  );
  MUXCY   \cpu6502/addr_gen/Madd_addr1_reg[7]_addr1_value_to_add[7]_add_2_OUT_cy<6>  (
    .CI(\cpu6502/addr_gen/Madd_addr1_reg[7]_addr1_value_to_add[7]_add_2_OUT_cy<5>_242 ),
    .DI(\cpu6502/addr_gen/addr1_reg [6]),
    .S(\cpu6502/addr_gen/Madd_addr1_reg[7]_addr1_value_to_add[7]_add_2_OUT_lut<6>_241 ),
    .O(\cpu6502/addr_gen/Madd_addr1_reg[7]_addr1_value_to_add[7]_add_2_OUT_cy<6>_240 )
  );
  XORCY   \cpu6502/addr_gen/Madd_addr1_reg[7]_addr1_value_to_add[7]_add_2_OUT_xor<5>  (
    .CI(\cpu6502/addr_gen/Madd_addr1_reg[7]_addr1_value_to_add[7]_add_2_OUT_cy<4>_244 ),
    .LI(\cpu6502/addr_gen/Madd_addr1_reg[7]_addr1_value_to_add[7]_add_2_OUT_lut<5>_243 ),
    .O(\cpu6502/addr_gen/addr1_reg[7]_addr1_value_to_add[7]_add_2_OUT<5> )
  );
  MUXCY   \cpu6502/addr_gen/Madd_addr1_reg[7]_addr1_value_to_add[7]_add_2_OUT_cy<5>  (
    .CI(\cpu6502/addr_gen/Madd_addr1_reg[7]_addr1_value_to_add[7]_add_2_OUT_cy<4>_244 ),
    .DI(\cpu6502/addr_gen/addr1_reg [5]),
    .S(\cpu6502/addr_gen/Madd_addr1_reg[7]_addr1_value_to_add[7]_add_2_OUT_lut<5>_243 ),
    .O(\cpu6502/addr_gen/Madd_addr1_reg[7]_addr1_value_to_add[7]_add_2_OUT_cy<5>_242 )
  );
  XORCY   \cpu6502/addr_gen/Madd_addr1_reg[7]_addr1_value_to_add[7]_add_2_OUT_xor<4>  (
    .CI(\cpu6502/addr_gen/Madd_addr1_reg[7]_addr1_value_to_add[7]_add_2_OUT_cy<3>_246 ),
    .LI(\cpu6502/addr_gen/Madd_addr1_reg[7]_addr1_value_to_add[7]_add_2_OUT_lut<4>_245 ),
    .O(\cpu6502/addr_gen/addr1_reg[7]_addr1_value_to_add[7]_add_2_OUT<4> )
  );
  MUXCY   \cpu6502/addr_gen/Madd_addr1_reg[7]_addr1_value_to_add[7]_add_2_OUT_cy<4>  (
    .CI(\cpu6502/addr_gen/Madd_addr1_reg[7]_addr1_value_to_add[7]_add_2_OUT_cy<3>_246 ),
    .DI(\cpu6502/addr_gen/addr1_reg [4]),
    .S(\cpu6502/addr_gen/Madd_addr1_reg[7]_addr1_value_to_add[7]_add_2_OUT_lut<4>_245 ),
    .O(\cpu6502/addr_gen/Madd_addr1_reg[7]_addr1_value_to_add[7]_add_2_OUT_cy<4>_244 )
  );
  XORCY   \cpu6502/addr_gen/Madd_addr1_reg[7]_addr1_value_to_add[7]_add_2_OUT_xor<3>  (
    .CI(\cpu6502/addr_gen/Madd_addr1_reg[7]_addr1_value_to_add[7]_add_2_OUT_cy<2>_248 ),
    .LI(\cpu6502/addr_gen/Madd_addr1_reg[7]_addr1_value_to_add[7]_add_2_OUT_lut<3>_247 ),
    .O(\cpu6502/addr_gen/addr1_reg[7]_addr1_value_to_add[7]_add_2_OUT<3> )
  );
  MUXCY   \cpu6502/addr_gen/Madd_addr1_reg[7]_addr1_value_to_add[7]_add_2_OUT_cy<3>  (
    .CI(\cpu6502/addr_gen/Madd_addr1_reg[7]_addr1_value_to_add[7]_add_2_OUT_cy<2>_248 ),
    .DI(\cpu6502/addr_gen/addr1_reg [3]),
    .S(\cpu6502/addr_gen/Madd_addr1_reg[7]_addr1_value_to_add[7]_add_2_OUT_lut<3>_247 ),
    .O(\cpu6502/addr_gen/Madd_addr1_reg[7]_addr1_value_to_add[7]_add_2_OUT_cy<3>_246 )
  );
  XORCY   \cpu6502/addr_gen/Madd_addr1_reg[7]_addr1_value_to_add[7]_add_2_OUT_xor<2>  (
    .CI(\cpu6502/addr_gen/Madd_addr1_reg[7]_addr1_value_to_add[7]_add_2_OUT_cy<1>_250 ),
    .LI(\cpu6502/addr_gen/Madd_addr1_reg[7]_addr1_value_to_add[7]_add_2_OUT_lut<2>_249 ),
    .O(\cpu6502/addr_gen/addr1_reg[7]_addr1_value_to_add[7]_add_2_OUT<2> )
  );
  MUXCY   \cpu6502/addr_gen/Madd_addr1_reg[7]_addr1_value_to_add[7]_add_2_OUT_cy<2>  (
    .CI(\cpu6502/addr_gen/Madd_addr1_reg[7]_addr1_value_to_add[7]_add_2_OUT_cy<1>_250 ),
    .DI(\cpu6502/addr_gen/addr1_reg [2]),
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
  \cpu6502/alu/Mcount_stack_ptr_reg_lut<1>  (
    .I0(\cpu6502/alu/dest_reg_sel[2]_PWR_6_o_equal_44_o_inv ),
    .I1(\cpu6502/alu/stack_ptr_reg [1]),
    .I2(\cpu6502/controller/stack_ctrl_signals [0]),
    .I3(\cpu6502/alu/alu_result [1]),
    .O(\cpu6502/alu/Mcount_stack_ptr_reg_lut [1])
  );
  MULT_AND   \cpu6502/alu/Mcount_stack_ptr_reg_mand_0  (
    .I0(\cpu6502/alu/stack_ptr_reg [1]),
    .I1(\cpu6502/alu/dest_reg_sel[2]_PWR_6_o_equal_44_o_inv ),
    .LO(\cpu6502/alu/Mcount_stack_ptr_reg_mand1 )
  );
  XORCY   \cpu6502/alu/Mcount_stack_ptr_reg_xor<0>  (
    .CI(\cpu6502/alu/Mcount_stack_ptr_reg ),
    .LI(\cpu6502/alu/Mcount_stack_ptr_reg_lut [0]),
    .O(\cpu6502/alu/Mcount_stack_ptr_reg1_500 )
  );
  MUXCY   \cpu6502/alu/Mcount_stack_ptr_reg_cy<0>  (
    .CI(\cpu6502/alu/Mcount_stack_ptr_reg ),
    .DI(\cpu6502/alu/Mcount_stack_ptr_reg_mand_501 ),
    .S(\cpu6502/alu/Mcount_stack_ptr_reg_lut [0]),
    .O(\cpu6502/alu/Mcount_stack_ptr_reg_cy [0])
  );
  LUT4 #(
    .INIT ( 16'h7D28 ))
  \cpu6502/alu/Mcount_stack_ptr_reg_lut<0>  (
    .I0(\cpu6502/alu/dest_reg_sel[2]_PWR_6_o_equal_44_o_inv ),
    .I1(\cpu6502/alu/stack_ptr_reg [0]),
    .I2(\cpu6502/controller/stack_ctrl_signals [0]),
    .I3(\cpu6502/alu/alu_result [0]),
    .O(\cpu6502/alu/Mcount_stack_ptr_reg_lut [0])
  );
  MULT_AND   \cpu6502/alu/Mcount_stack_ptr_reg_mand  (
    .I0(\cpu6502/alu/stack_ptr_reg [0]),
    .I1(\cpu6502/alu/dest_reg_sel[2]_PWR_6_o_equal_44_o_inv ),
    .LO(\cpu6502/alu/Mcount_stack_ptr_reg_mand_501 )
  );
  FDRE #(
    .INIT ( 1'b0 ))
  \cpu6502/alu/n_flag  (
    .C(clk),
    .CE(\cpu6502/alu/_n0237_inv ),
    .D(\cpu6502/alu/n_flag_mem_in[7]_MUX_185_o ),
    .R(rst),
    .Q(\cpu6502/alu/n_flag_86 )
  );
  FDRE   \cpu6502/alu/result_reg_7  (
    .C(clk),
    .CE(\cpu6502/alu_en ),
    .D(\cpu6502/alu/alu_result [7]),
    .R(rst),
    .Q(\cpu6502/alu/result_reg [7])
  );
  FDRE   \cpu6502/alu/result_reg_6  (
    .C(clk),
    .CE(\cpu6502/alu_en ),
    .D(\cpu6502/alu/alu_result [6]),
    .R(rst),
    .Q(\cpu6502/alu/result_reg [6])
  );
  FDRE   \cpu6502/alu/result_reg_5  (
    .C(clk),
    .CE(\cpu6502/alu_en ),
    .D(\cpu6502/alu/alu_result [5]),
    .R(rst),
    .Q(\cpu6502/alu/result_reg [5])
  );
  FDRE   \cpu6502/alu/result_reg_4  (
    .C(clk),
    .CE(\cpu6502/alu_en ),
    .D(\cpu6502/alu/alu_result [4]),
    .R(rst),
    .Q(\cpu6502/alu/result_reg [4])
  );
  FDRE   \cpu6502/alu/result_reg_3  (
    .C(clk),
    .CE(\cpu6502/alu_en ),
    .D(\cpu6502/alu/alu_result [3]),
    .R(rst),
    .Q(\cpu6502/alu/result_reg [3])
  );
  FDRE   \cpu6502/alu/result_reg_2  (
    .C(clk),
    .CE(\cpu6502/alu_en ),
    .D(\cpu6502/alu/alu_result [2]),
    .R(rst),
    .Q(\cpu6502/alu/result_reg [2])
  );
  FDRE   \cpu6502/alu/result_reg_1  (
    .C(clk),
    .CE(\cpu6502/alu_en ),
    .D(\cpu6502/alu/alu_result [1]),
    .R(rst),
    .Q(\cpu6502/alu/result_reg [1])
  );
  FDRE   \cpu6502/alu/result_reg_0  (
    .C(clk),
    .CE(\cpu6502/alu_en ),
    .D(\cpu6502/alu/alu_result [0]),
    .R(rst),
    .Q(\cpu6502/alu/result_reg [0])
  );
  FDRE   \cpu6502/alu/y_reg_7  (
    .C(clk),
    .CE(\cpu6502/alu/alu_enable_dest_reg_sel[2]_AND_87_o ),
    .D(\cpu6502/alu/alu_result [7]),
    .R(rst),
    .Q(\cpu6502/alu/y_reg [7])
  );
  FDRE   \cpu6502/alu/y_reg_6  (
    .C(clk),
    .CE(\cpu6502/alu/alu_enable_dest_reg_sel[2]_AND_87_o ),
    .D(\cpu6502/alu/alu_result [6]),
    .R(rst),
    .Q(\cpu6502/alu/y_reg [6])
  );
  FDRE   \cpu6502/alu/y_reg_5  (
    .C(clk),
    .CE(\cpu6502/alu/alu_enable_dest_reg_sel[2]_AND_87_o ),
    .D(\cpu6502/alu/alu_result [5]),
    .R(rst),
    .Q(\cpu6502/alu/y_reg [5])
  );
  FDRE   \cpu6502/alu/y_reg_4  (
    .C(clk),
    .CE(\cpu6502/alu/alu_enable_dest_reg_sel[2]_AND_87_o ),
    .D(\cpu6502/alu/alu_result [4]),
    .R(rst),
    .Q(\cpu6502/alu/y_reg [4])
  );
  FDRE   \cpu6502/alu/y_reg_3  (
    .C(clk),
    .CE(\cpu6502/alu/alu_enable_dest_reg_sel[2]_AND_87_o ),
    .D(\cpu6502/alu/alu_result [3]),
    .R(rst),
    .Q(\cpu6502/alu/y_reg [3])
  );
  FDRE   \cpu6502/alu/y_reg_2  (
    .C(clk),
    .CE(\cpu6502/alu/alu_enable_dest_reg_sel[2]_AND_87_o ),
    .D(\cpu6502/alu/alu_result [2]),
    .R(rst),
    .Q(\cpu6502/alu/y_reg [2])
  );
  FDRE   \cpu6502/alu/y_reg_1  (
    .C(clk),
    .CE(\cpu6502/alu/alu_enable_dest_reg_sel[2]_AND_87_o ),
    .D(\cpu6502/alu/alu_result [1]),
    .R(rst),
    .Q(\cpu6502/alu/y_reg [1])
  );
  FDRE   \cpu6502/alu/y_reg_0  (
    .C(clk),
    .CE(\cpu6502/alu/alu_enable_dest_reg_sel[2]_AND_87_o ),
    .D(\cpu6502/alu/alu_result [0]),
    .R(rst),
    .Q(\cpu6502/alu/y_reg [0])
  );
  FDRE   \cpu6502/alu/x_reg_7  (
    .C(clk),
    .CE(\cpu6502/alu/alu_enable_dest_reg_sel[2]_AND_86_o ),
    .D(\cpu6502/alu/alu_result [7]),
    .R(rst),
    .Q(\cpu6502/alu/x_reg [7])
  );
  FDRE   \cpu6502/alu/x_reg_6  (
    .C(clk),
    .CE(\cpu6502/alu/alu_enable_dest_reg_sel[2]_AND_86_o ),
    .D(\cpu6502/alu/alu_result [6]),
    .R(rst),
    .Q(\cpu6502/alu/x_reg [6])
  );
  FDRE   \cpu6502/alu/x_reg_5  (
    .C(clk),
    .CE(\cpu6502/alu/alu_enable_dest_reg_sel[2]_AND_86_o ),
    .D(\cpu6502/alu/alu_result [5]),
    .R(rst),
    .Q(\cpu6502/alu/x_reg [5])
  );
  FDRE   \cpu6502/alu/x_reg_4  (
    .C(clk),
    .CE(\cpu6502/alu/alu_enable_dest_reg_sel[2]_AND_86_o ),
    .D(\cpu6502/alu/alu_result [4]),
    .R(rst),
    .Q(\cpu6502/alu/x_reg [4])
  );
  FDRE   \cpu6502/alu/x_reg_3  (
    .C(clk),
    .CE(\cpu6502/alu/alu_enable_dest_reg_sel[2]_AND_86_o ),
    .D(\cpu6502/alu/alu_result [3]),
    .R(rst),
    .Q(\cpu6502/alu/x_reg [3])
  );
  FDRE   \cpu6502/alu/x_reg_2  (
    .C(clk),
    .CE(\cpu6502/alu/alu_enable_dest_reg_sel[2]_AND_86_o ),
    .D(\cpu6502/alu/alu_result [2]),
    .R(rst),
    .Q(\cpu6502/alu/x_reg [2])
  );
  FDRE   \cpu6502/alu/x_reg_1  (
    .C(clk),
    .CE(\cpu6502/alu/alu_enable_dest_reg_sel[2]_AND_86_o ),
    .D(\cpu6502/alu/alu_result [1]),
    .R(rst),
    .Q(\cpu6502/alu/x_reg [1])
  );
  FDRE   \cpu6502/alu/x_reg_0  (
    .C(clk),
    .CE(\cpu6502/alu/alu_enable_dest_reg_sel[2]_AND_86_o ),
    .D(\cpu6502/alu/alu_result [0]),
    .R(rst),
    .Q(\cpu6502/alu/x_reg [0])
  );
  FDRE   \cpu6502/alu/accumulator_7  (
    .C(clk),
    .CE(\cpu6502/alu/alu_enable_dest_reg_sel[2]_AND_85_o ),
    .D(\cpu6502/alu/alu_result [7]),
    .R(rst),
    .Q(\cpu6502/alu/accumulator [7])
  );
  FDRE   \cpu6502/alu/accumulator_6  (
    .C(clk),
    .CE(\cpu6502/alu/alu_enable_dest_reg_sel[2]_AND_85_o ),
    .D(\cpu6502/alu/alu_result [6]),
    .R(rst),
    .Q(\cpu6502/alu/accumulator [6])
  );
  FDRE   \cpu6502/alu/accumulator_5  (
    .C(clk),
    .CE(\cpu6502/alu/alu_enable_dest_reg_sel[2]_AND_85_o ),
    .D(\cpu6502/alu/alu_result [5]),
    .R(rst),
    .Q(\cpu6502/alu/accumulator [5])
  );
  FDRE   \cpu6502/alu/accumulator_4  (
    .C(clk),
    .CE(\cpu6502/alu/alu_enable_dest_reg_sel[2]_AND_85_o ),
    .D(\cpu6502/alu/alu_result [4]),
    .R(rst),
    .Q(\cpu6502/alu/accumulator [4])
  );
  FDRE   \cpu6502/alu/accumulator_3  (
    .C(clk),
    .CE(\cpu6502/alu/alu_enable_dest_reg_sel[2]_AND_85_o ),
    .D(\cpu6502/alu/alu_result [3]),
    .R(rst),
    .Q(\cpu6502/alu/accumulator [3])
  );
  FDRE   \cpu6502/alu/accumulator_2  (
    .C(clk),
    .CE(\cpu6502/alu/alu_enable_dest_reg_sel[2]_AND_85_o ),
    .D(\cpu6502/alu/alu_result [2]),
    .R(rst),
    .Q(\cpu6502/alu/accumulator [2])
  );
  FDRE   \cpu6502/alu/accumulator_1  (
    .C(clk),
    .CE(\cpu6502/alu/alu_enable_dest_reg_sel[2]_AND_85_o ),
    .D(\cpu6502/alu/alu_result [1]),
    .R(rst),
    .Q(\cpu6502/alu/accumulator [1])
  );
  FDRE   \cpu6502/alu/accumulator_0  (
    .C(clk),
    .CE(\cpu6502/alu/alu_enable_dest_reg_sel[2]_AND_85_o ),
    .D(\cpu6502/alu/alu_result [0]),
    .R(rst),
    .Q(\cpu6502/alu/accumulator [0])
  );
  FDRE #(
    .INIT ( 1'b0 ))
  \cpu6502/alu/d_flag  (
    .C(clk),
    .CE(\cpu6502/alu_en ),
    .D(\cpu6502/alu/status_op[1]_mem_in[3]_MUX_176_o ),
    .R(rst),
    .Q(\cpu6502/alu/d_flag_84 )
  );
  FDRE #(
    .INIT ( 1'b0 ))
  \cpu6502/alu/z_flag  (
    .C(clk),
    .CE(\cpu6502/alu/_n0227_inv ),
    .D(\cpu6502/alu/z_flag_mem_in[1]_MUX_166_o ),
    .R(rst),
    .Q(\cpu6502/alu/z_flag_82 )
  );
  FDRE #(
    .INIT ( 1'b0 ))
  \cpu6502/alu/v_flag  (
    .C(clk),
    .CE(\cpu6502/alu_en ),
    .D(\cpu6502/alu/status_op[1]_mem_in[6]_MUX_181_o ),
    .R(rst),
    .Q(\cpu6502/alu/v_flag_85 )
  );
  LUT3 #(
    .INIT ( 8'h80 ))
  \cpu6502/alu_en11  (
    .I0(\cpu6502/controller/set_next_state_127 ),
    .I1(ph2_falling),
    .I2(\cpu6502/controller/alu_enable_131 ),
    .O(\cpu6502/alu_en )
  );
  LUT3 #(
    .INIT ( 8'h80 ))
  \cpu6502/decoder/_n003511  (
    .I0(\cpu6502/controller/set_next_state_127 ),
    .I1(ph2_falling),
    .I2(\cpu6502/controller/inst_reg_clr_144 ),
    .O(\cpu6502/decoder/_n0035 )
  );
  LUT4 #(
    .INIT ( 16'h57FF ))
  \cpu6502/decoder/_n0040_01  (
    .I0(\cpu6502/controller/set_next_state_127 ),
    .I1(\cpu6502/controller/inst_reg_we_143 ),
    .I2(\cpu6502/controller/inst_reg_clr_144 ),
    .I3(ph2_falling),
    .O(\cpu6502/decoder/_n0040_0 )
  );
  LUT3 #(
    .INIT ( 8'h80 ))
  \cpu6502/ph2_falling_mem_din_reg_we_AND_63_o11  (
    .I0(\cpu6502/controller/set_next_state_127 ),
    .I1(ph2_falling),
    .I2(\cpu6502/controller/mem_din_reg_we_130 ),
    .O(\cpu6502/ph2_falling_mem_din_reg_we_AND_63_o )
  );
  LUT6 #(
    .INIT ( 64'hCCCCFF00AAAAF0F0 ))
  \cpu6502/Mmux_address_sel[1]_addr_zp[15]_wide_mux_6_OUT91  (
    .I0(\cpu6502/addr_gen/addr2_l_reg [2]),
    .I1(\cpu6502/addr_gen/addr1_reg [2]),
    .I2(\cpu6502/pc/pc [2]),
    .I3(\cpu6502/alu/stack_ptr_reg [2]),
    .I4(\cpu6502/address_sel [1]),
    .I5(\cpu6502/address_sel [0]),
    .O(\cpu6502/address_sel[1]_addr_zp[15]_wide_mux_6_OUT<2> )
  );
  LUT6 #(
    .INIT ( 64'hCCCCFF00AAAAF0F0 ))
  \cpu6502/Mmux_address_sel[1]_addr_zp[15]_wide_mux_6_OUT81  (
    .I0(\cpu6502/addr_gen/addr2_l_reg [1]),
    .I1(\cpu6502/addr_gen/addr1_reg [1]),
    .I2(\cpu6502/pc/pc [1]),
    .I3(\cpu6502/alu/stack_ptr_reg [1]),
    .I4(\cpu6502/address_sel [1]),
    .I5(\cpu6502/address_sel [0]),
    .O(\cpu6502/address_sel[1]_addr_zp[15]_wide_mux_6_OUT<1> )
  );
  LUT6 #(
    .INIT ( 64'hCCCCFF00AAAAF0F0 ))
  \cpu6502/Mmux_address_sel[1]_addr_zp[15]_wide_mux_6_OUT141  (
    .I0(\cpu6502/addr_gen/addr2_l_reg [7]),
    .I1(\cpu6502/addr_gen/addr1_reg [7]),
    .I2(\cpu6502/pc/pc [7]),
    .I3(\cpu6502/alu/stack_ptr_reg [7]),
    .I4(\cpu6502/address_sel [1]),
    .I5(\cpu6502/address_sel [0]),
    .O(\cpu6502/address_sel[1]_addr_zp[15]_wide_mux_6_OUT<7> )
  );
  LUT6 #(
    .INIT ( 64'hCCCCFF00AAAAF0F0 ))
  \cpu6502/Mmux_address_sel[1]_addr_zp[15]_wide_mux_6_OUT131  (
    .I0(\cpu6502/addr_gen/addr2_l_reg [6]),
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
    .I2(\cpu6502/controller/set_next_state_127 ),
    .I3(\cpu6502/operation_type [1]),
    .I4(\cpu6502/operation_type [2]),
    .I5(\cpu6502/controller/current_state_FSM_FFd8_302 ),
    .O(\cpu6502/controller/current_state_FSM_FFd8-In )
  );
  LUT6 #(
    .INIT ( 64'h2AEA2A2A2A2A2A2A ))
  \cpu6502/controller/current_state_FSM_FFd14-In1  (
    .I0(\cpu6502/controller/current_state_FSM_FFd14_380 ),
    .I1(ph2_rising),
    .I2(\cpu6502/controller/set_next_state_127 ),
    .I3(\cpu6502/controller/addr_mode[2]_GND_4_o_equal_25_o ),
    .I4(\cpu6502/controller/current_state_FSM_FFd25-In22 ),
    .I5(\cpu6502/operation_type [2]),
    .O(\cpu6502/controller/current_state_FSM_FFd14-In )
  );
  LUT4 #(
    .INIT ( 16'hFFFE ))
  \cpu6502/controller/current_state__n04371  (
    .I0(\cpu6502/controller/current_state_FSM_FFd3_384 ),
    .I1(\cpu6502/controller/current_state_FSM_FFd17_386 ),
    .I2(\cpu6502/controller/current_state_FSM_FFd4_385 ),
    .I3(\cpu6502/controller/current_state_FSM_FFd16_387 ),
    .O(\cpu6502/controller/_n0437 )
  );
  LUT5 #(
    .INIT ( 32'hFFFF0200 ))
  \cpu6502/controller/current_state_current_state[4]_operation_type[2]_Select_182_o1  (
    .I0(\cpu6502/controller/current_state_FSM_FFd3_384 ),
    .I1(\cpu6502/operation_type [2]),
    .I2(\cpu6502/operation_type [1]),
    .I3(\cpu6502/operation_type [0]),
    .I4(\cpu6502/controller/current_state_FSM_FFd16_387 ),
    .O(\cpu6502/controller/current_state[4]_operation_type[2]_Select_182_o )
  );
  LUT5 #(
    .INIT ( 32'hFFFFFFFE ))
  \cpu6502/controller/current_state_address_sel<1>1  (
    .I0(\cpu6502/controller/current_state_FSM_FFd12_356 ),
    .I1(\cpu6502/controller/current_state_FSM_FFd21_304 ),
    .I2(\cpu6502/controller/current_state_FSM_FFd11_148 ),
    .I3(\cpu6502/controller/current_state_FSM_FFd20_388 ),
    .I4(\cpu6502/controller/current_state_address_sel<0>2_299 ),
    .O(\cpu6502/address_sel [1])
  );
  LUT5 #(
    .INIT ( 32'h2A2AEA2A ))
  \cpu6502/controller/current_state_FSM_FFd24-In1  (
    .I0(\cpu6502/controller/current_state_FSM_FFd24_382 ),
    .I1(\cpu6502/controller/set_next_state_127 ),
    .I2(ph2_rising),
    .I3(\cpu6502/controller/current_state_FSM_FFd25_383 ),
    .I4(\cpu6502/controller/is_interrupt ),
    .O(\cpu6502/controller/current_state_FSM_FFd24-In )
  );
  LUT4 #(
    .INIT ( 16'h0001 ))
  \cpu6502/controller/current_state[4]_reduce_nor_174_o1  (
    .I0(\cpu6502/controller/current_state_FSM_FFd23_358 ),
    .I1(\cpu6502/controller/current_state_FSM_FFd17_386 ),
    .I2(\cpu6502/controller/current_state_FSM_FFd4_385 ),
    .I3(\cpu6502/controller/current_state_FSM_FFd11_148 ),
    .O(\cpu6502/controller/current_state[4]_reduce_nor_174_o )
  );
  LUT6 #(
    .INIT ( 64'hFEFEFEEEEEEEEEEE ))
  \cpu6502/controller/current_state_address_sel<0>21  (
    .I0(\cpu6502/controller/current_state_FSM_FFd19_303 ),
    .I1(\cpu6502/controller/current_state_FSM_FFd18_343 ),
    .I2(\cpu6502/controller/current_state_FSM_FFd22_357 ),
    .I3(\cpu6502/addr_mode [1]),
    .I4(\cpu6502/addr_mode [0]),
    .I5(\cpu6502/addr_mode [2]),
    .O(\cpu6502/controller/current_state_address_sel<0>2_299 )
  );
  LUT6 #(
    .INIT ( 64'hABAAAAAAAAAAAAAA ))
  \cpu6502/controller/current_state_FSM_FFd20-In1111  (
    .I0(\cpu6502/controller/current_state_FSM_FFd12_356 ),
    .I1(\cpu6502/addr_mode [2]),
    .I2(\cpu6502/operation_type [2]),
    .I3(\cpu6502/addr_mode [0]),
    .I4(\cpu6502/addr_mode [1]),
    .I5(\cpu6502/controller/current_state_FSM_FFd25-In22 ),
    .O(\cpu6502/controller/current_state_FSM_FFd20-In111 )
  );
  LUT6 #(
    .INIT ( 64'hFFFFF77788888000 ))
  \cpu6502/controller/current_state_FSM_FFd5-In1  (
    .I0(ph2_rising),
    .I1(\cpu6502/controller/set_next_state_127 ),
    .I2(\cpu6502/controller/current_state_FSM_FFd4_385 ),
    .I3(\cpu6502/controller/operation_type[2]_PWR_4_o_equal_130_o ),
    .I4(\cpu6502/controller/current_state_FSM_FFd6_379 ),
    .I5(\cpu6502/controller/current_state_FSM_FFd5_378 ),
    .O(\cpu6502/controller/current_state_FSM_FFd5-In )
  );
  LUT6 #(
    .INIT ( 64'hFF2AFF2AFF2A2A2A ))
  \cpu6502/controller/current_state_FSM_FFd15-In1  (
    .I0(\cpu6502/controller/current_state_FSM_FFd15_375 ),
    .I1(ph2_rising),
    .I2(\cpu6502/controller/set_next_state_127 ),
    .I3(\cpu6502/controller/current_state_FSM_FFd16-In1 ),
    .I4(\cpu6502/operation_type [0]),
    .I5(\cpu6502/operation_type [2]),
    .O(\cpu6502/controller/current_state_FSM_FFd15-In )
  );
  LUT4 #(
    .INIT ( 16'hEA2A ))
  \cpu6502/controller/current_state_FSM_FFd2-In1  (
    .I0(\cpu6502/controller/current_state_FSM_FFd2_377 ),
    .I1(ph2_rising),
    .I2(\cpu6502/controller/set_next_state_127 ),
    .I3(\cpu6502/controller/current_state_FSM_FFd10_373 ),
    .O(\cpu6502/controller/current_state_FSM_FFd2-In )
  );
  LUT5 #(
    .INIT ( 32'h2A2AEA2A ))
  \cpu6502/controller/current_state_FSM_FFd3-In1  (
    .I0(\cpu6502/controller/current_state_FSM_FFd3_384 ),
    .I1(\cpu6502/controller/set_next_state_127 ),
    .I2(ph2_rising),
    .I3(\cpu6502/controller/current_state_FSM_FFd4_385 ),
    .I4(\cpu6502/controller/operation_type[2]_PWR_4_o_equal_130_o ),
    .O(\cpu6502/controller/current_state_FSM_FFd3-In )
  );
  LUT4 #(
    .INIT ( 16'hEA2A ))
  \cpu6502/controller/current_state_FSM_FFd4-In1  (
    .I0(\cpu6502/controller/current_state_FSM_FFd4_385 ),
    .I1(ph2_rising),
    .I2(\cpu6502/controller/set_next_state_127 ),
    .I3(\cpu6502/controller/current_state_FSM_FFd17_386 ),
    .O(\cpu6502/controller/current_state_FSM_FFd4-In )
  );
  LUT6 #(
    .INIT ( 64'h2A2A2A2A2A2AFF2A ))
  \cpu6502/controller/current_state_FSM_FFd16-In2  (
    .I0(\cpu6502/controller/current_state_FSM_FFd16_387 ),
    .I1(ph2_rising),
    .I2(\cpu6502/controller/set_next_state_127 ),
    .I3(\cpu6502/controller/current_state_FSM_FFd16-In1 ),
    .I4(\cpu6502/operation_type [0]),
    .I5(\cpu6502/operation_type [2]),
    .O(\cpu6502/controller/current_state_FSM_FFd16-In )
  );
  LUT5 #(
    .INIT ( 32'h80880080 ))
  \cpu6502/controller/current_state_current_state[4]_GND_4_o_select_152_OUT<6>1  (
    .I0(\cpu6502/controller/_n0556 ),
    .I1(\cpu6502/controller/current_state_current_state[4]_GND_4_o_select_152_OUT<1>1_300 ),
    .I2(\cpu6502/addr_mode [2]),
    .I3(\cpu6502/addr_mode [0]),
    .I4(\cpu6502/addr_mode [1]),
    .O(\cpu6502/controller/current_state[4]_GND_4_o_select_152_OUT<6> )
  );
  LUT3 #(
    .INIT ( 8'hA8 ))
  \cpu6502/controller/current_state_current_state[4]_GND_4_o_select_152_OUT<7>1  (
    .I0(\cpu6502/addr_gen/address_carry_165 ),
    .I1(\cpu6502/controller/current_state_FSM_FFd12_356 ),
    .I2(\cpu6502/controller/current_state_FSM_FFd21_304 ),
    .O(\cpu6502/controller/current_state[4]_GND_4_o_select_152_OUT<7> )
  );
  LUT5 #(
    .INIT ( 32'h80000080 ))
  \cpu6502/controller/current_state_current_state[4]_GND_4_o_select_152_OUT<5>1  (
    .I0(\cpu6502/controller/_n0556 ),
    .I1(\cpu6502/addr_mode [2]),
    .I2(\cpu6502/controller/current_state_current_state[4]_GND_4_o_select_152_OUT<1>1_300 ),
    .I3(\cpu6502/addr_mode [0]),
    .I4(\cpu6502/addr_mode [1]),
    .O(\cpu6502/controller/current_state[4]_GND_4_o_select_152_OUT<5> )
  );
  LUT3 #(
    .INIT ( 8'h02 ))
  \cpu6502/controller/current_state_FSM_FFd25-In221  (
    .I0(\cpu6502/controller/current_state_FSM_FFd24_382 ),
    .I1(\cpu6502/operation_type [1]),
    .I2(\cpu6502/operation_type [0]),
    .O(\cpu6502/controller/current_state_FSM_FFd25-In22 )
  );
  LUT4 #(
    .INIT ( 16'h8000 ))
  \cpu6502/controller/current_state_FSM_FFd16-In11  (
    .I0(\cpu6502/controller/set_next_state_127 ),
    .I1(ph2_rising),
    .I2(\cpu6502/controller/current_state_FSM_FFd24_382 ),
    .I3(\cpu6502/operation_type [1]),
    .O(\cpu6502/controller/current_state_FSM_FFd16-In1 )
  );
  LUT3 #(
    .INIT ( 8'hFE ))
  \cpu6502/controller/current_state__n04251  (
    .I0(\cpu6502/controller/current_state_FSM_FFd5_378 ),
    .I1(\cpu6502/controller/current_state_FSM_FFd14_380 ),
    .I2(\cpu6502/controller/current_state_FSM_FFd2_377 ),
    .O(\cpu6502/controller/_n0425 )
  );
  LUT3 #(
    .INIT ( 8'hFE ))
  \cpu6502/controller/current_state__n04331  (
    .I0(\cpu6502/controller/current_state_FSM_FFd10_373 ),
    .I1(\cpu6502/controller/current_state_FSM_FFd15_375 ),
    .I2(\cpu6502/controller/current_state_FSM_FFd9_374 ),
    .O(\cpu6502/controller/_n0433 )
  );
  LUT3 #(
    .INIT ( 8'hFE ))
  \cpu6502/controller/current_state__n05561  (
    .I0(\cpu6502/controller/current_state_FSM_FFd13_381 ),
    .I1(\cpu6502/controller/current_state_FSM_FFd22_357 ),
    .I2(\cpu6502/controller/current_state_FSM_FFd3_384 ),
    .O(\cpu6502/controller/_n0556 )
  );
  LUT2 #(
    .INIT ( 4'hE ))
  \cpu6502/controller/current_state_data_out_sel<1>1  (
    .I0(\cpu6502/controller/current_state_FSM_FFd4_385 ),
    .I1(\cpu6502/controller/current_state_FSM_FFd17_386 ),
    .O(\cpu6502/data_out_sel [1])
  );
  LUT4 #(
    .INIT ( 16'hFEEE ))
  \cpu6502/controller/current_state_data_out_sel<0>1  (
    .I0(\cpu6502/controller/current_state_FSM_FFd17_386 ),
    .I1(\cpu6502/controller/current_state_FSM_FFd3_384 ),
    .I2(\cpu6502/controller/current_state_FSM_FFd16_387 ),
    .I3(\cpu6502/sreg_to_dout ),
    .O(\cpu6502/data_out_sel [0])
  );
  LUT2 #(
    .INIT ( 4'h8 ))
  \cpu6502/controller/current_state_ph1_falling_current_state[4]_AND_34_o1  (
    .I0(\cpu6502/controller/current_state_FSM_FFd17_386 ),
    .I1(ph1_falling),
    .O(\cpu6502/controller/ph1_falling_current_state[4]_AND_34_o )
  );
  LUT3 #(
    .INIT ( 8'h80 ))
  \cpu6502/controller/current_state_ph2_rising_nmi_recognized_AND_11_o1  (
    .I0(\cpu6502/controller/current_state_FSM_FFd3_384 ),
    .I1(\cpu6502/controller/nmi_recognized_369 ),
    .I2(ph2_rising),
    .O(\cpu6502/controller/ph2_rising_nmi_recognized_AND_11_o )
  );
  LUT5 #(
    .INIT ( 32'hFFFF0800 ))
  \cpu6502/controller/current_state_current_state[4]_GND_4_o_select_152_OUT<3>1  (
    .I0(\cpu6502/controller/current_state_FSM_FFd22_357 ),
    .I1(\cpu6502/addr_mode [2]),
    .I2(\cpu6502/addr_mode [1]),
    .I3(\cpu6502/addr_mode [0]),
    .I4(\cpu6502/controller/current_state_FSM_FFd19_303 ),
    .O(\cpu6502/controller/current_state[4]_GND_4_o_select_152_OUT<3> )
  );
  LUT2 #(
    .INIT ( 4'hD ))
  \cpu6502/controller/Mram_rst_active_PWR_4_o_wide_mux_92_OUT21  (
    .I0(\cpu6502/controller/nmi_active_370 ),
    .I1(\cpu6502/controller/rst_active_389 ),
    .O(\cpu6502/controller/Mram_rst_active_PWR_4_o_wide_mux_92_OUT2 )
  );
  LUT3 #(
    .INIT ( 8'hBA ))
  \cpu6502/controller/Reset_OR_DriverANDClockEnable11  (
    .I0(rst),
    .I1(\cpu6502/controller/current_state_FSM_FFd25_383 ),
    .I2(ph1_falling),
    .O(\cpu6502/controller/Reset_OR_DriverANDClockEnable1_336 )
  );
  LUT3 #(
    .INIT ( 8'hBA ))
  \cpu6502/controller/Reset_OR_DriverANDClockEnable1  (
    .I0(rst),
    .I1(\cpu6502/controller/current_state_FSM_FFd6_379 ),
    .I2(ph1_falling),
    .O(\cpu6502/controller/Reset_OR_DriverANDClockEnable )
  );
  LUT4 #(
    .INIT ( 16'hFFAE ))
  \cpu6502/controller/is_interrupt1  (
    .I0(\cpu6502/controller/nmi_active_370 ),
    .I1(\cpu6502/controller/int_active_371 ),
    .I2(\cpu6502/alu/i_flag_83 ),
    .I3(\cpu6502/controller/rst_active_389 ),
    .O(\cpu6502/controller/is_interrupt )
  );
  LUT3 #(
    .INIT ( 8'h20 ))
  \cpu6502/controller/operation_type[2]_PWR_4_o_equal_130_o<2>1  (
    .I0(\cpu6502/operation_type [0]),
    .I1(\cpu6502/operation_type [1]),
    .I2(\cpu6502/operation_type [2]),
    .O(\cpu6502/controller/operation_type[2]_PWR_4_o_equal_130_o )
  );
  LUT3 #(
    .INIT ( 8'h02 ))
  \cpu6502/controller/operation_type[2]_PWR_4_o_equal_90_o<2>1  (
    .I0(\cpu6502/operation_type [2]),
    .I1(\cpu6502/operation_type [1]),
    .I2(\cpu6502/operation_type [0]),
    .O(\cpu6502/controller/operation_type[2]_PWR_4_o_equal_90_o )
  );
  LUT3 #(
    .INIT ( 8'h02 ))
  \cpu6502/controller/addr_mode[2]_GND_4_o_equal_25_o<2>1  (
    .I0(\cpu6502/addr_mode [0]),
    .I1(\cpu6502/addr_mode [2]),
    .I2(\cpu6502/addr_mode [1]),
    .O(\cpu6502/controller/addr_mode[2]_GND_4_o_equal_25_o )
  );
  LUT2 #(
    .INIT ( 4'hD ))
  \cpu6502/controller/ready_mem_rnw_OR_4_o1  (
    .I0(\NlwRenamedSig_OI_cpu6502/controller/mem_rnw ),
    .I1(ready),
    .O(\cpu6502/controller/ready_mem_rnw_OR_4_o )
  );
  LUT2 #(
    .INIT ( 4'h8 ))
  \cpu6502/controller/ph1_falling_set_next_state_AND_61_o1  (
    .I0(ph1_falling),
    .I1(\cpu6502/controller/set_next_state_127 ),
    .O(\cpu6502/controller/ph1_falling_set_next_state_AND_61_o )
  );
  LUT2 #(
    .INIT ( 4'hE ))
  \cpu6502/controller/rst_set_i_flag_OR_110_o1  (
    .I0(rst),
    .I1(\cpu6502/controller/set_i_flag_129 ),
    .O(\cpu6502/controller/rst_set_i_flag_OR_110_o )
  );
  LUT4 #(
    .INIT ( 16'h5410 ))
  \cpu6502/pc/value_to_load<0>1  (
    .I0(\cpu6502/controller/pc_operation [2]),
    .I1(\cpu6502/controller/pc_operation [1]),
    .I2(\cpu6502/pc/n0067 [0]),
    .I3(\cpu6502/mem_din_reg [0]),
    .O(\cpu6502/pc/value_to_load [0])
  );
  LUT5 #(
    .INIT ( 32'hEFEA4540 ))
  \cpu6502/pc/value_to_load<1>1  (
    .I0(\cpu6502/controller/pc_operation [2]),
    .I1(\cpu6502/mem_din_reg [1]),
    .I2(\cpu6502/controller/pc_operation [1]),
    .I3(\cpu6502/pc/n0067 [1]),
    .I4(\cpu6502/controller/vector_to_load [1]),
    .O(\cpu6502/pc/value_to_load [1])
  );
  LUT5 #(
    .INIT ( 32'hEFEA4540 ))
  \cpu6502/pc/value_to_load<2>1  (
    .I0(\cpu6502/controller/pc_operation [2]),
    .I1(\cpu6502/mem_din_reg [2]),
    .I2(\cpu6502/controller/pc_operation [1]),
    .I3(\cpu6502/pc/n0067 [2]),
    .I4(\cpu6502/controller/vector_to_load [2]),
    .O(\cpu6502/pc/value_to_load [2])
  );
  LUT4 #(
    .INIT ( 16'hFEF4 ))
  \cpu6502/pc/value_to_load<3>1  (
    .I0(\cpu6502/controller/pc_operation [1]),
    .I1(\cpu6502/pc/n0067 [3]),
    .I2(\cpu6502/controller/pc_operation [2]),
    .I3(\cpu6502/mem_din_reg [3]),
    .O(\cpu6502/pc/value_to_load [3])
  );
  LUT4 #(
    .INIT ( 16'hFEF4 ))
  \cpu6502/pc/value_to_load<4>1  (
    .I0(\cpu6502/controller/pc_operation [1]),
    .I1(\cpu6502/pc/n0067 [4]),
    .I2(\cpu6502/controller/pc_operation [2]),
    .I3(\cpu6502/mem_din_reg [4]),
    .O(\cpu6502/pc/value_to_load [4])
  );
  LUT4 #(
    .INIT ( 16'hFEF4 ))
  \cpu6502/pc/value_to_load<5>1  (
    .I0(\cpu6502/controller/pc_operation [1]),
    .I1(\cpu6502/pc/n0067 [5]),
    .I2(\cpu6502/controller/pc_operation [2]),
    .I3(\cpu6502/mem_din_reg [5]),
    .O(\cpu6502/pc/value_to_load [5])
  );
  LUT4 #(
    .INIT ( 16'hFEF4 ))
  \cpu6502/pc/value_to_load<6>1  (
    .I0(\cpu6502/controller/pc_operation [1]),
    .I1(\cpu6502/pc/n0067 [6]),
    .I2(\cpu6502/controller/pc_operation [2]),
    .I3(\cpu6502/mem_din_reg [6]),
    .O(\cpu6502/pc/value_to_load [6])
  );
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
